Meisterschulen-am-Ostbahnhof-Munchen/ISOBUS_Hardware/Hutschienenmoped-XL/8530697758676959232-8530697224823242752-365263750140063748.png

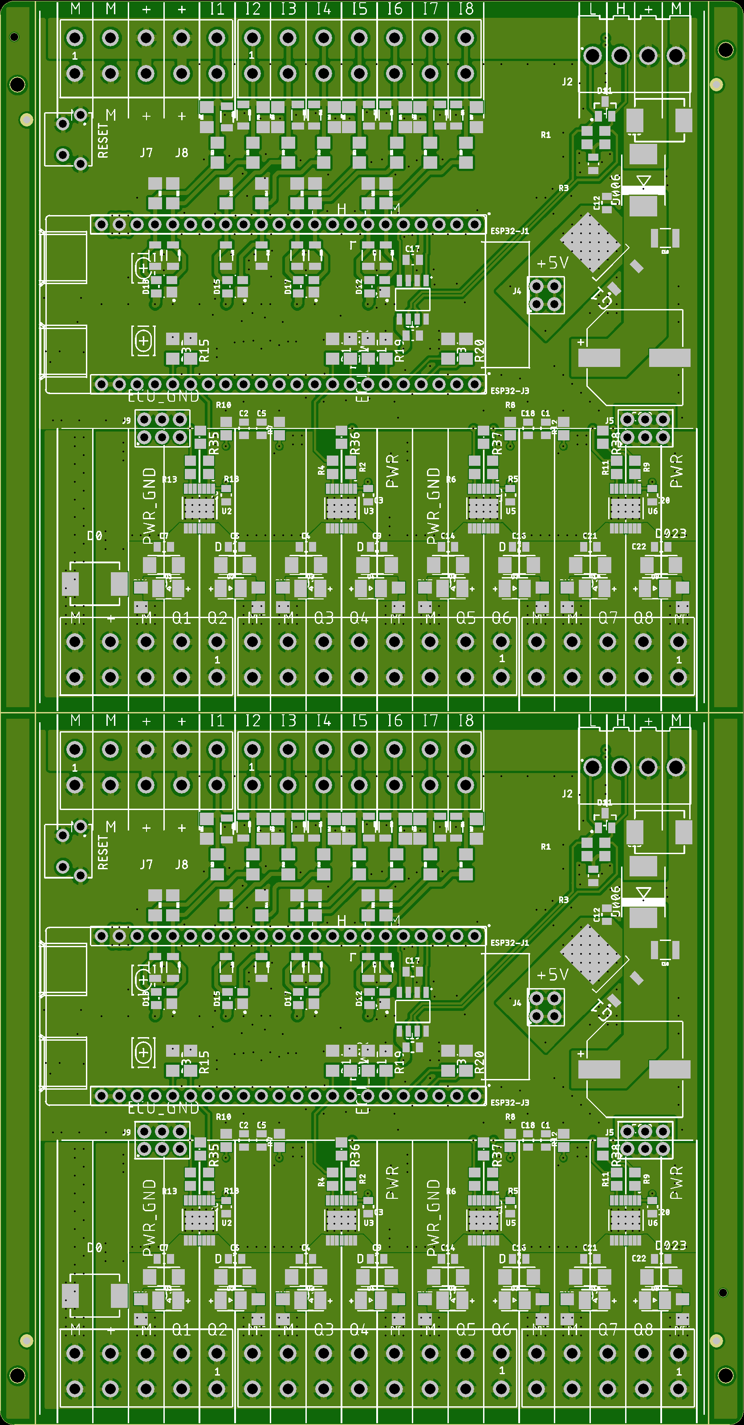
Hutschienenmoped-XL/8530697758676959232-8530697224823242752-365263750140063748.png
