Meisterschulen-am-Ostbahnhof-Munchen/ISOBUS_Hardware/Hutschienenmoped-XL/8530697765534781440-8530697225381355520-365263750140063747.png

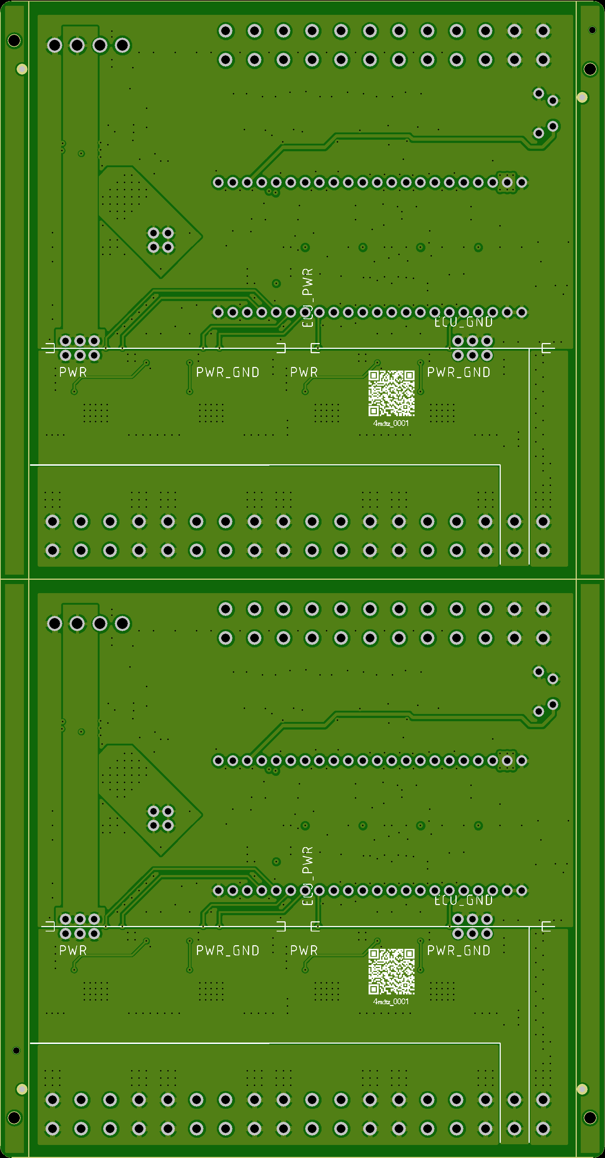
Hutschienenmoped-XL/8530697765534781440-8530697225381355520-365263750140063747.png
