Meisterschulen-am-Ostbahnhof-Munchen/ISOBUS_Hardware/XL-accessories/Board_4_Buttons/3D/Riegel rechts oben.stl

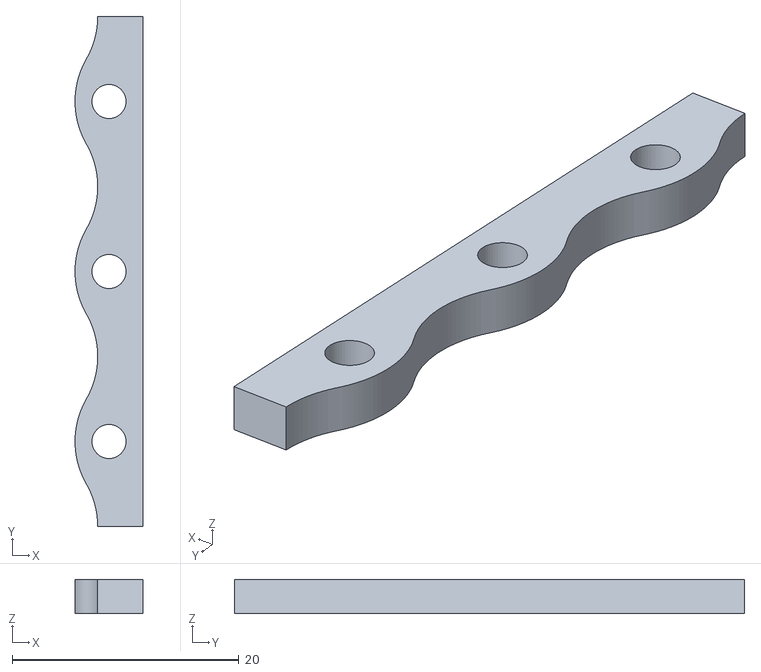
[picture p22: CAD file, 2024-10-04]
XL-accessories/Board_4_Buttons/3D/Riegel rechts oben.stl
6.00 x 45.0 x 3.00
