Meisterschulen-am-Ostbahnhof-Munchen/ISOBUS_Hardware/XL-accessories/Board_4_Buttons/Board_4_Buttons_WS-TASV.pdf

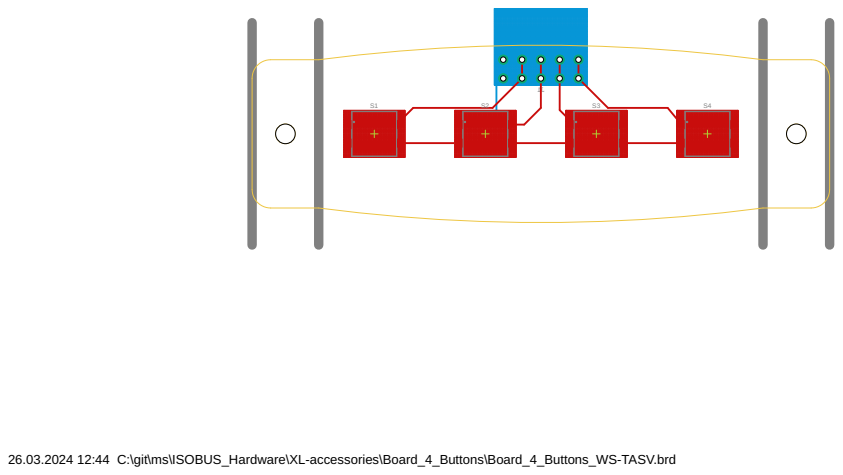
[picture p45: page 1]

26.03.2024 12:44 C:\git\ms\ISOBUS_Hardware\XL-accessories\Board_4_Buttons\Board_4_Buttons_WS-TASV.brd
