Meisterschulen-am-Ostbahnhof-Munchen/ISOBUS_Hardware/XL-accessories/Board_4_Buttons/Board_4_Buttons_WS-TATV.pdf

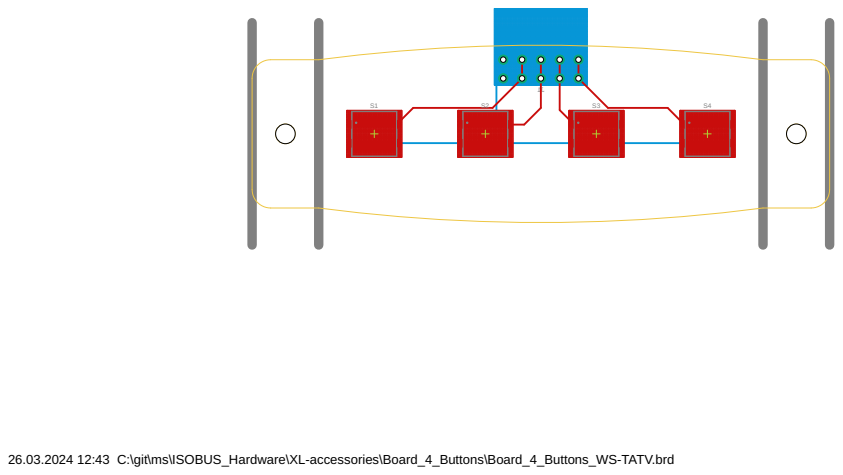
[picture p46: page 1]

26.03.2024 12:43 C:\git\ms\ISOBUS_Hardware\XL-accessories\Board_4_Buttons\Board_4_Buttons_WS-TATV.brd
