Meisterschulen-am-Ostbahnhof-Munchen/ISOBUS_Hardware/Hutschienenmoped-XL/Hauptplatine/Hauptplatine.pdf

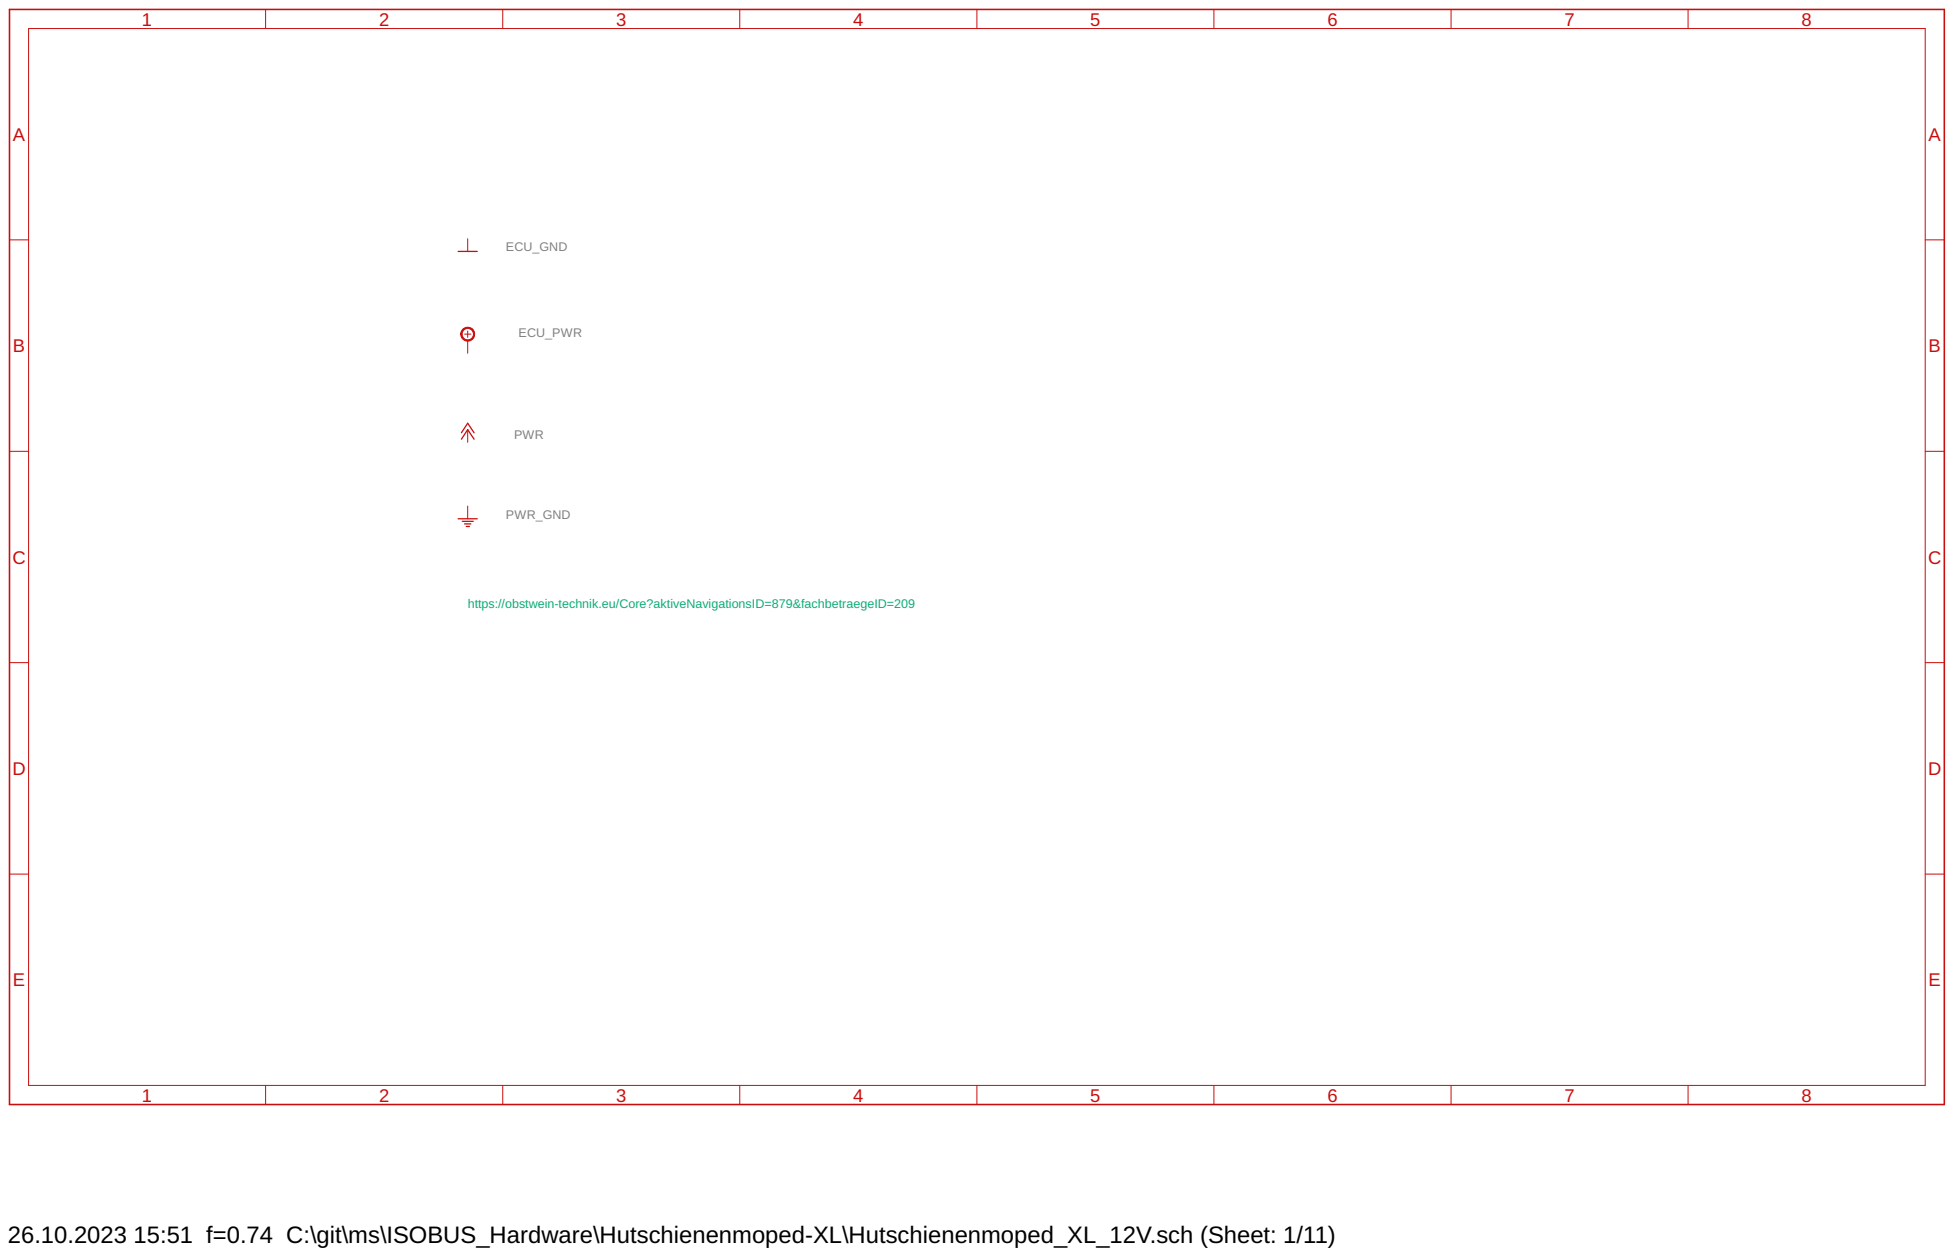
[picture p47: page 1]

https://obstwein-technik.eu/Core?aktiveNavigationsID=879&fachbetraegeID=209

26.10.2023 15:51 f=0.74 C:\git\ms\ISOBUS_Hardware\Hutschienenmoped-XL\Hutschienenmoped_XL_12V.sch (Sheet: 1/11)

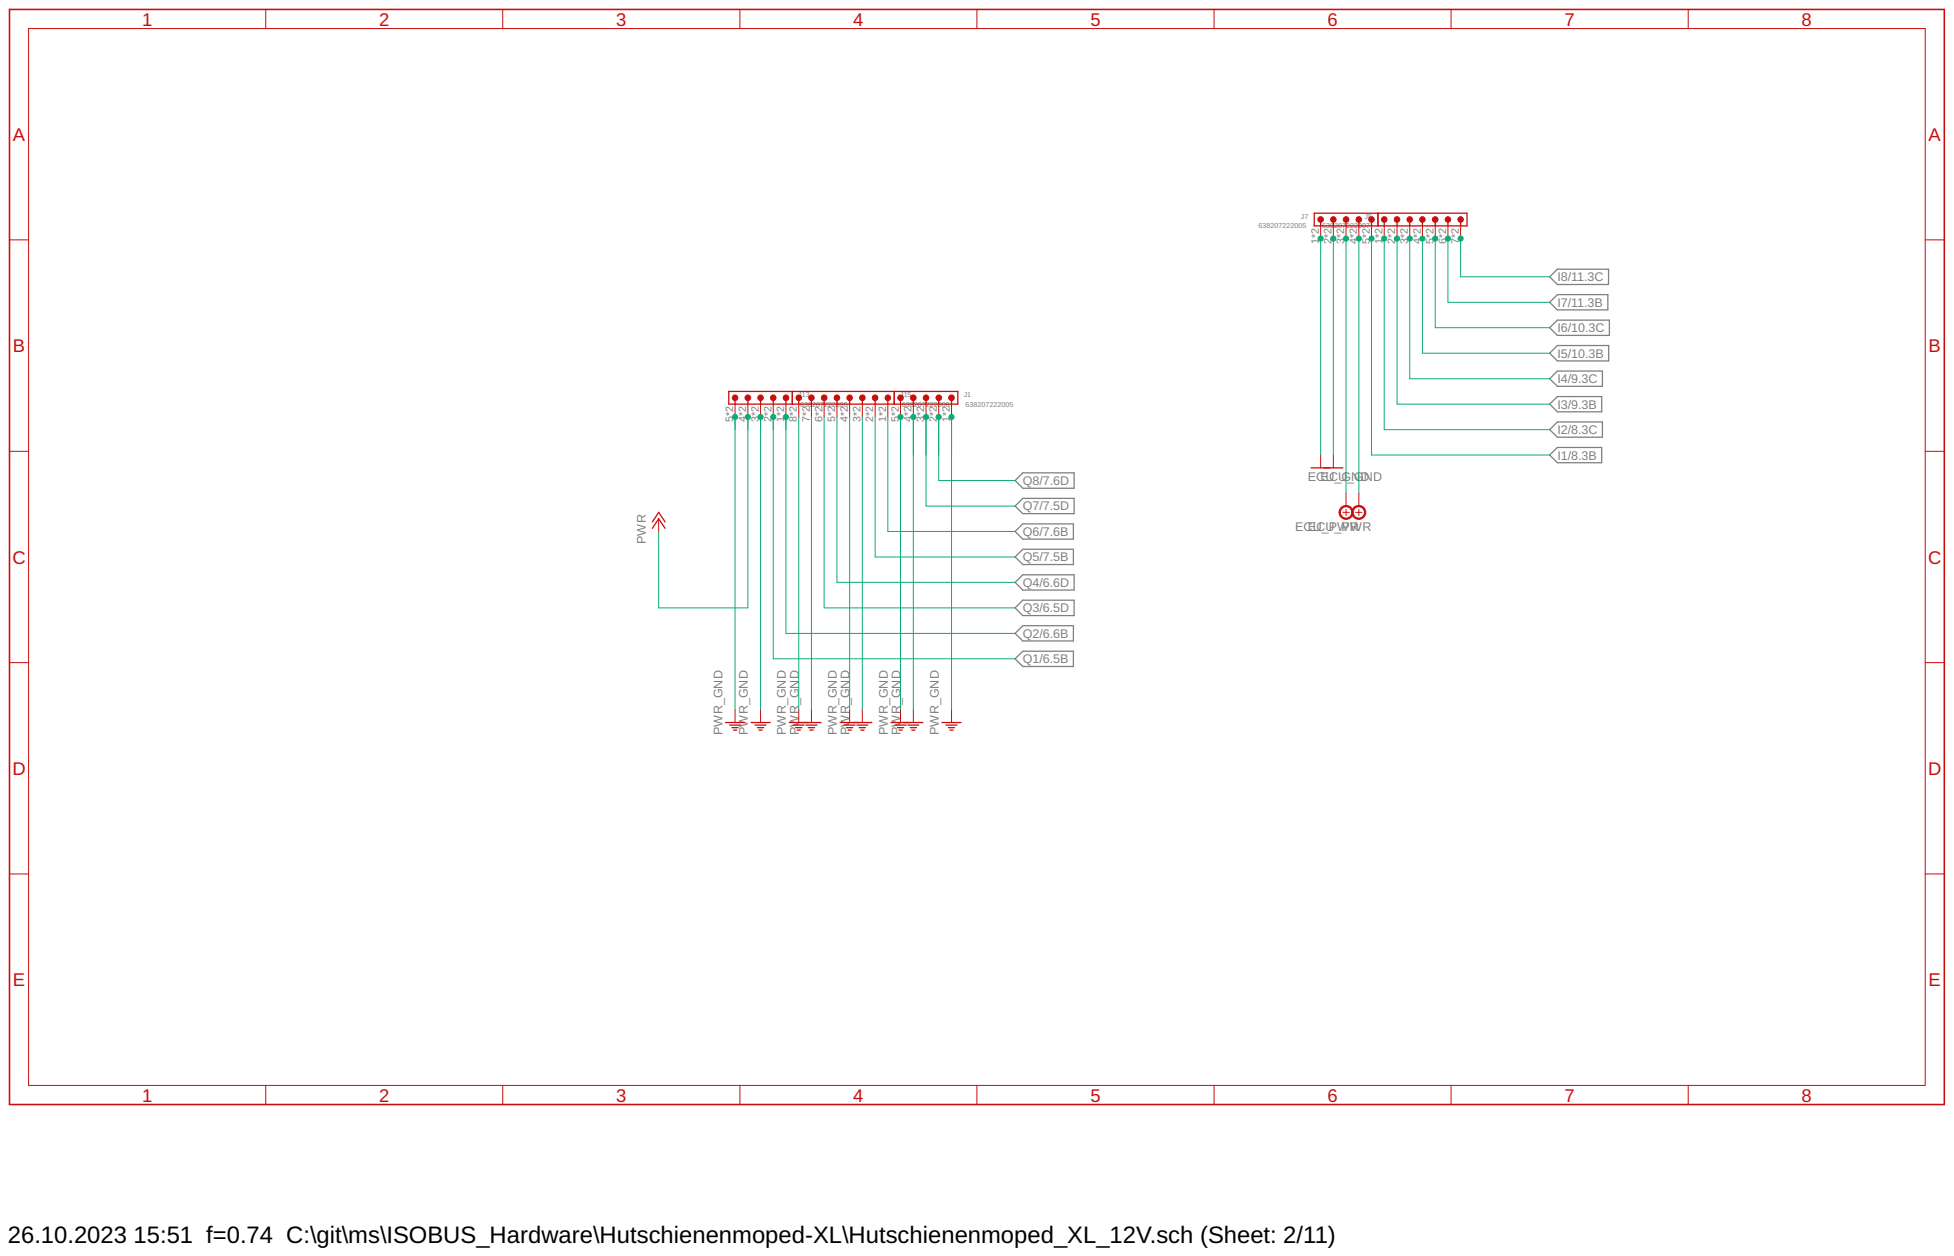
[picture p48: page 2]

26.10.2023 15:51 f=0.74 C:\git\ms\ISOBUS_Hardware\Hutschienenmoped-XL\Hutschienenmoped_XL_12V.sch (Sheet: 2/11)

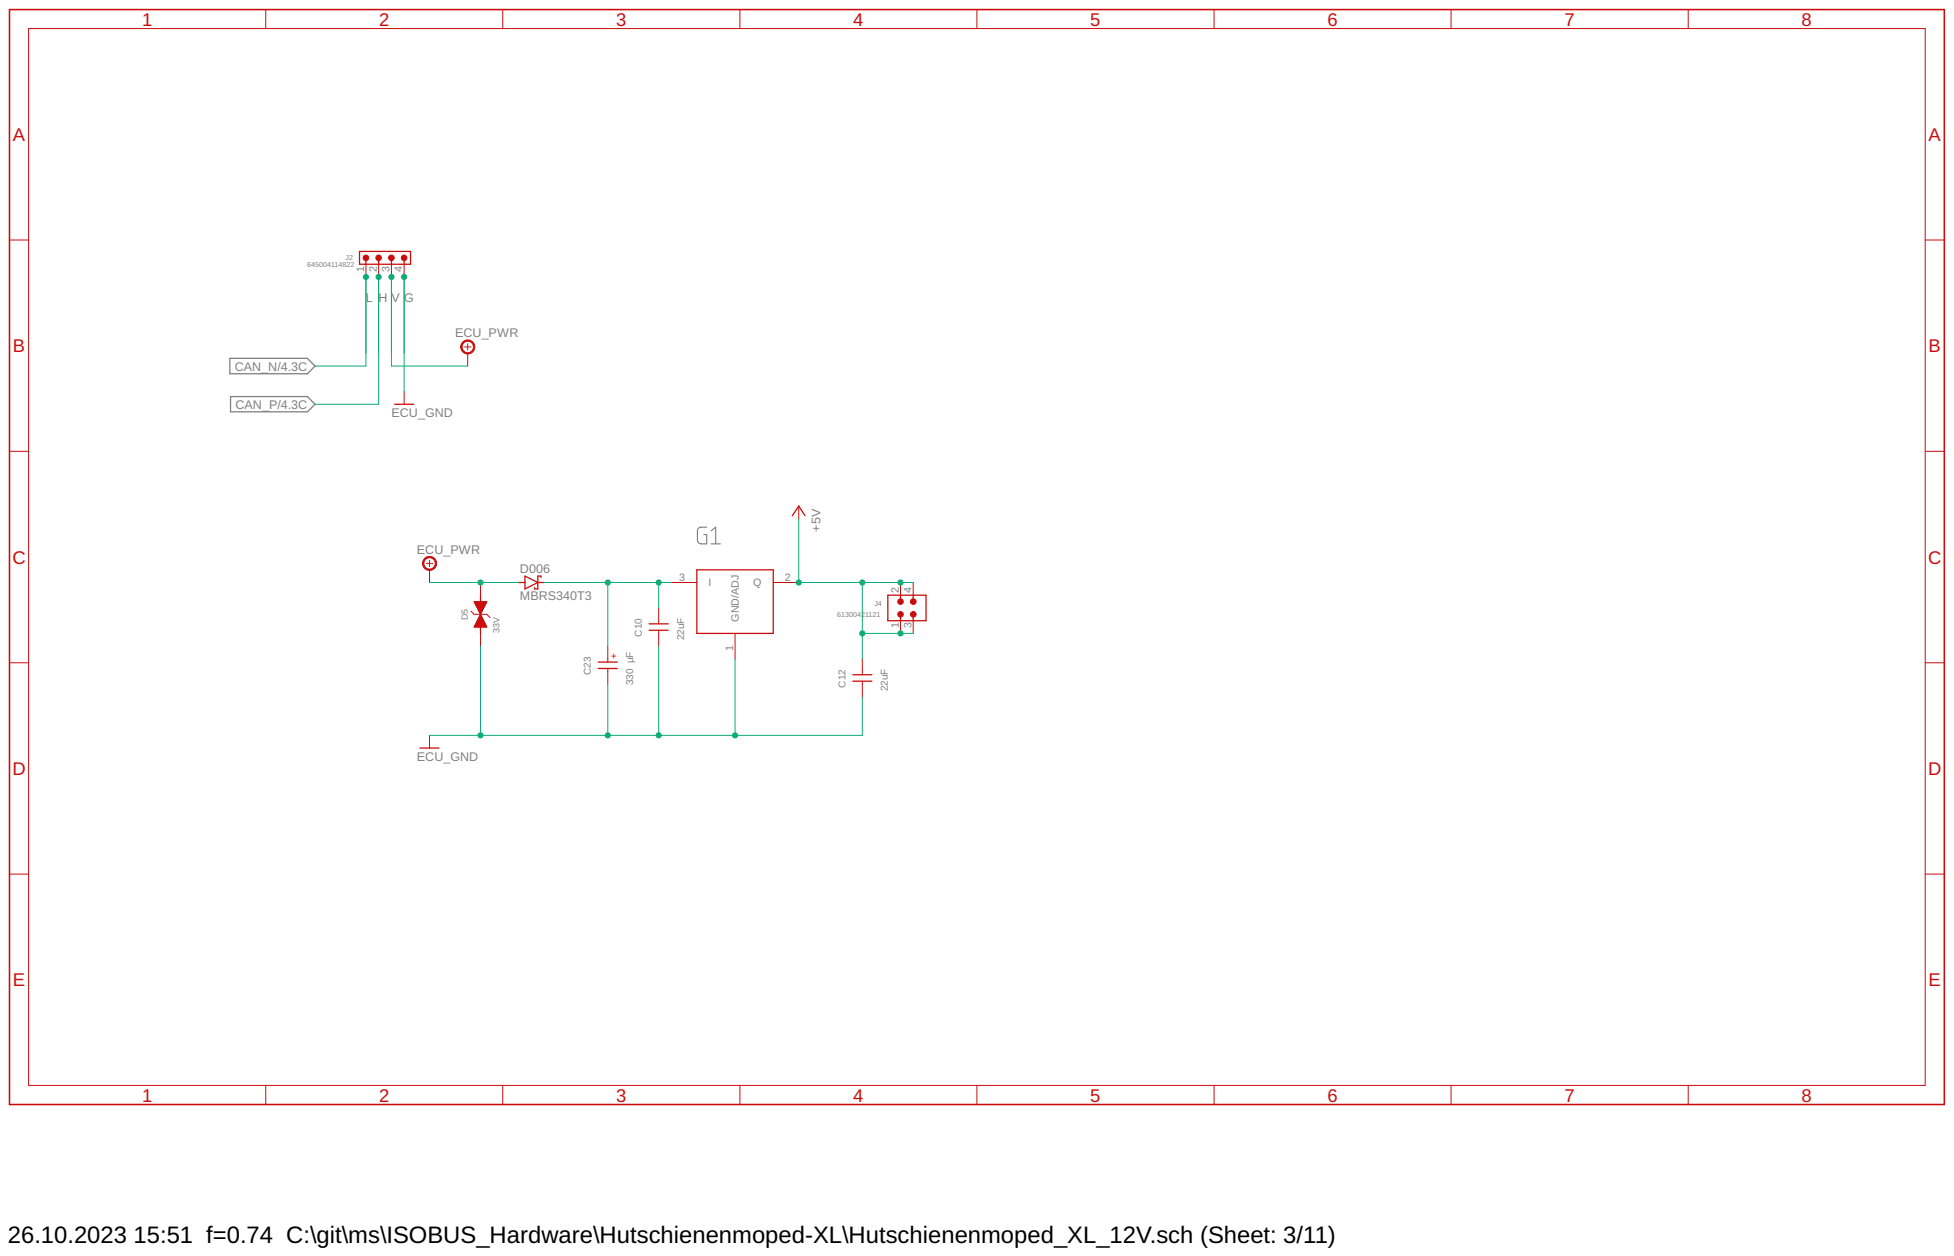
[picture p49: page 3]

26.10.2023 15:51 f=0.74 C:\git\ms\ISOBUS_Hardware\Hutschienenmoped-XL\Hutschienenmoped_XL_12V.sch (Sheet: 3/11)

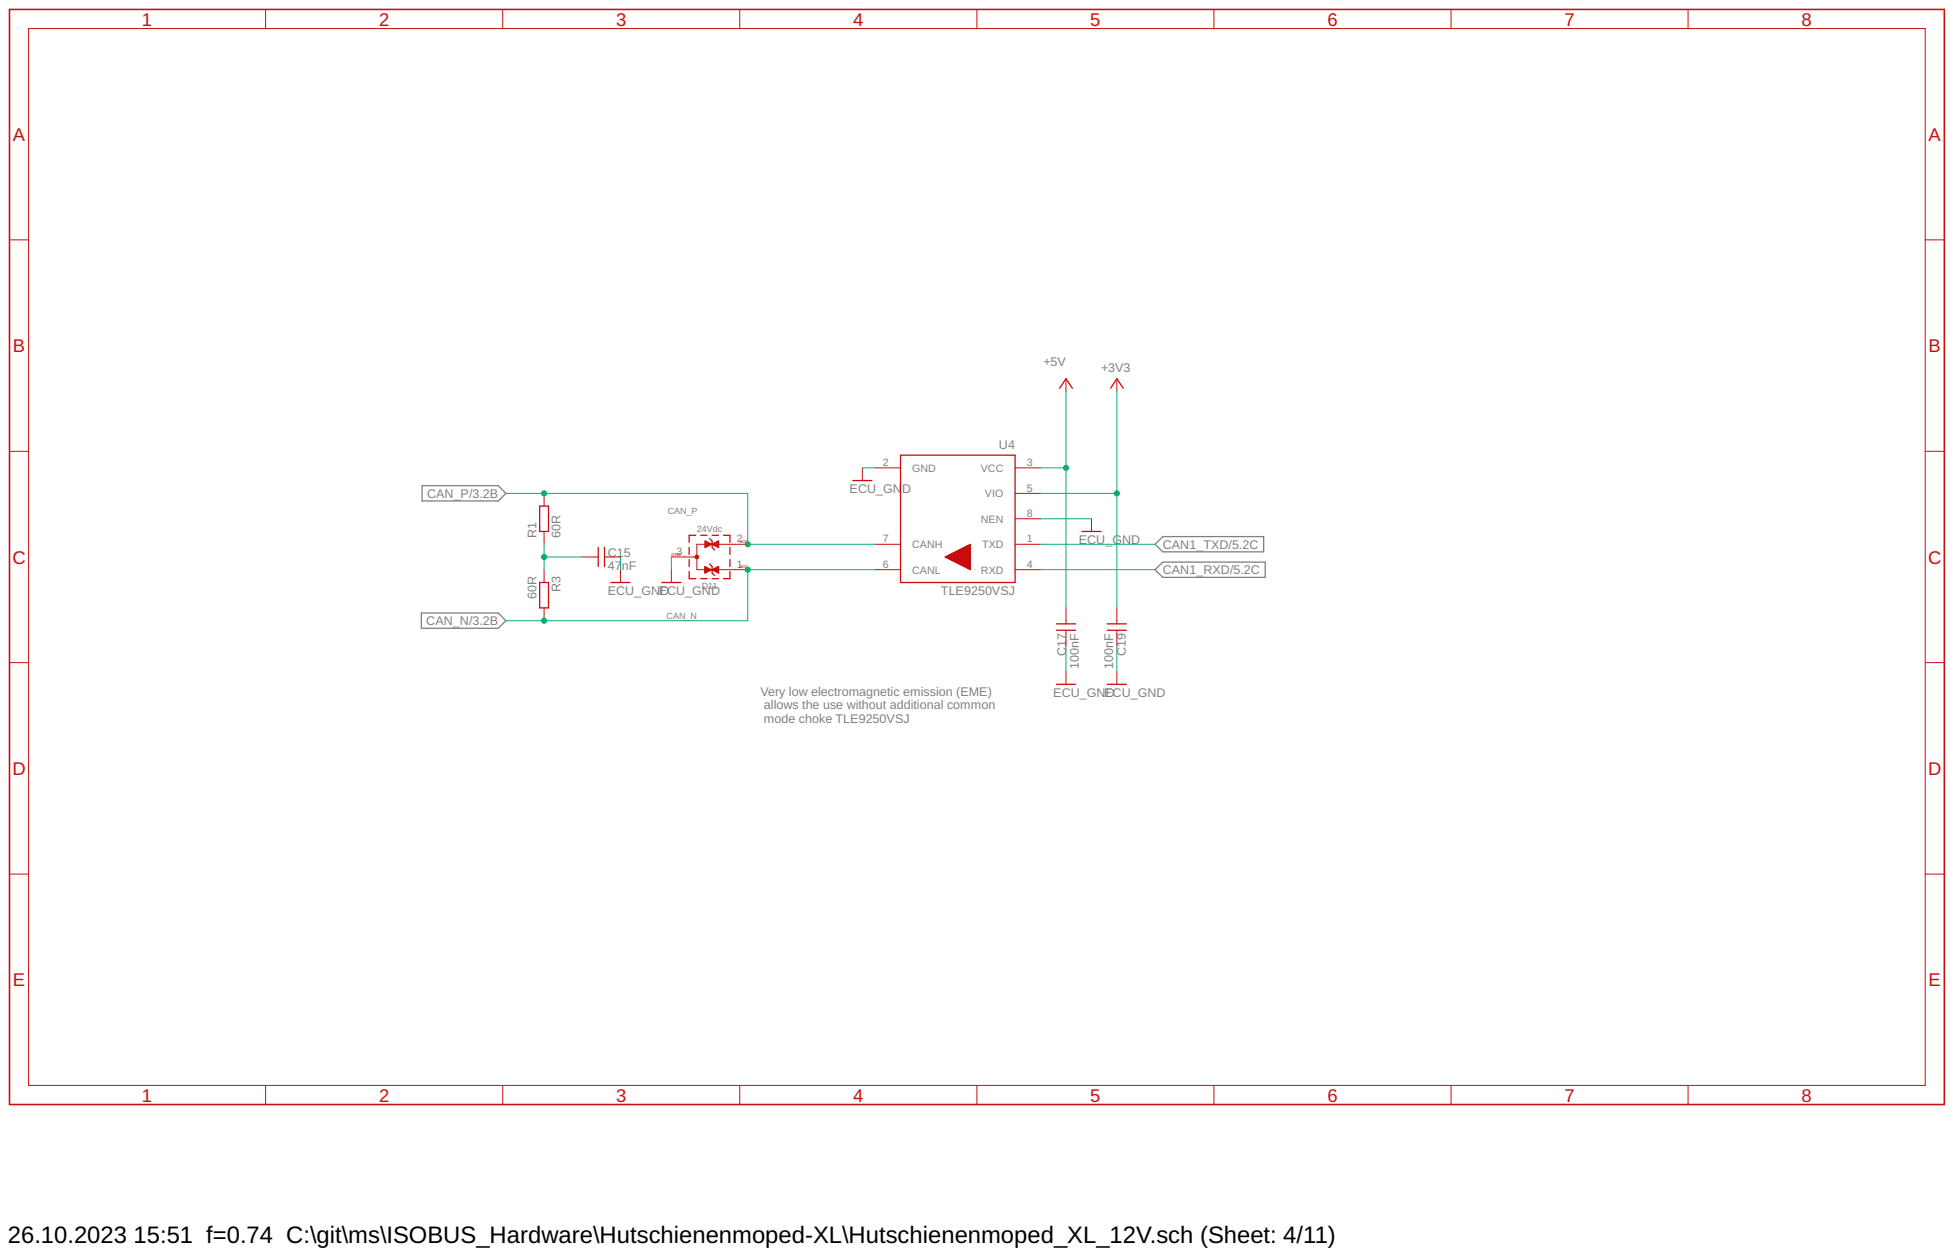
[picture p50: page 4]

Very low electromagnetic emission (EME) allows the use without additional common mode choke TLE9250VSJ

26.10.2023 15:51 f=0.74 C:\git\ms\ISOBUS_Hardware\Hutschienenmoped-XL\Hutschienenmoped_XL_12V.sch (Sheet: 4/11)

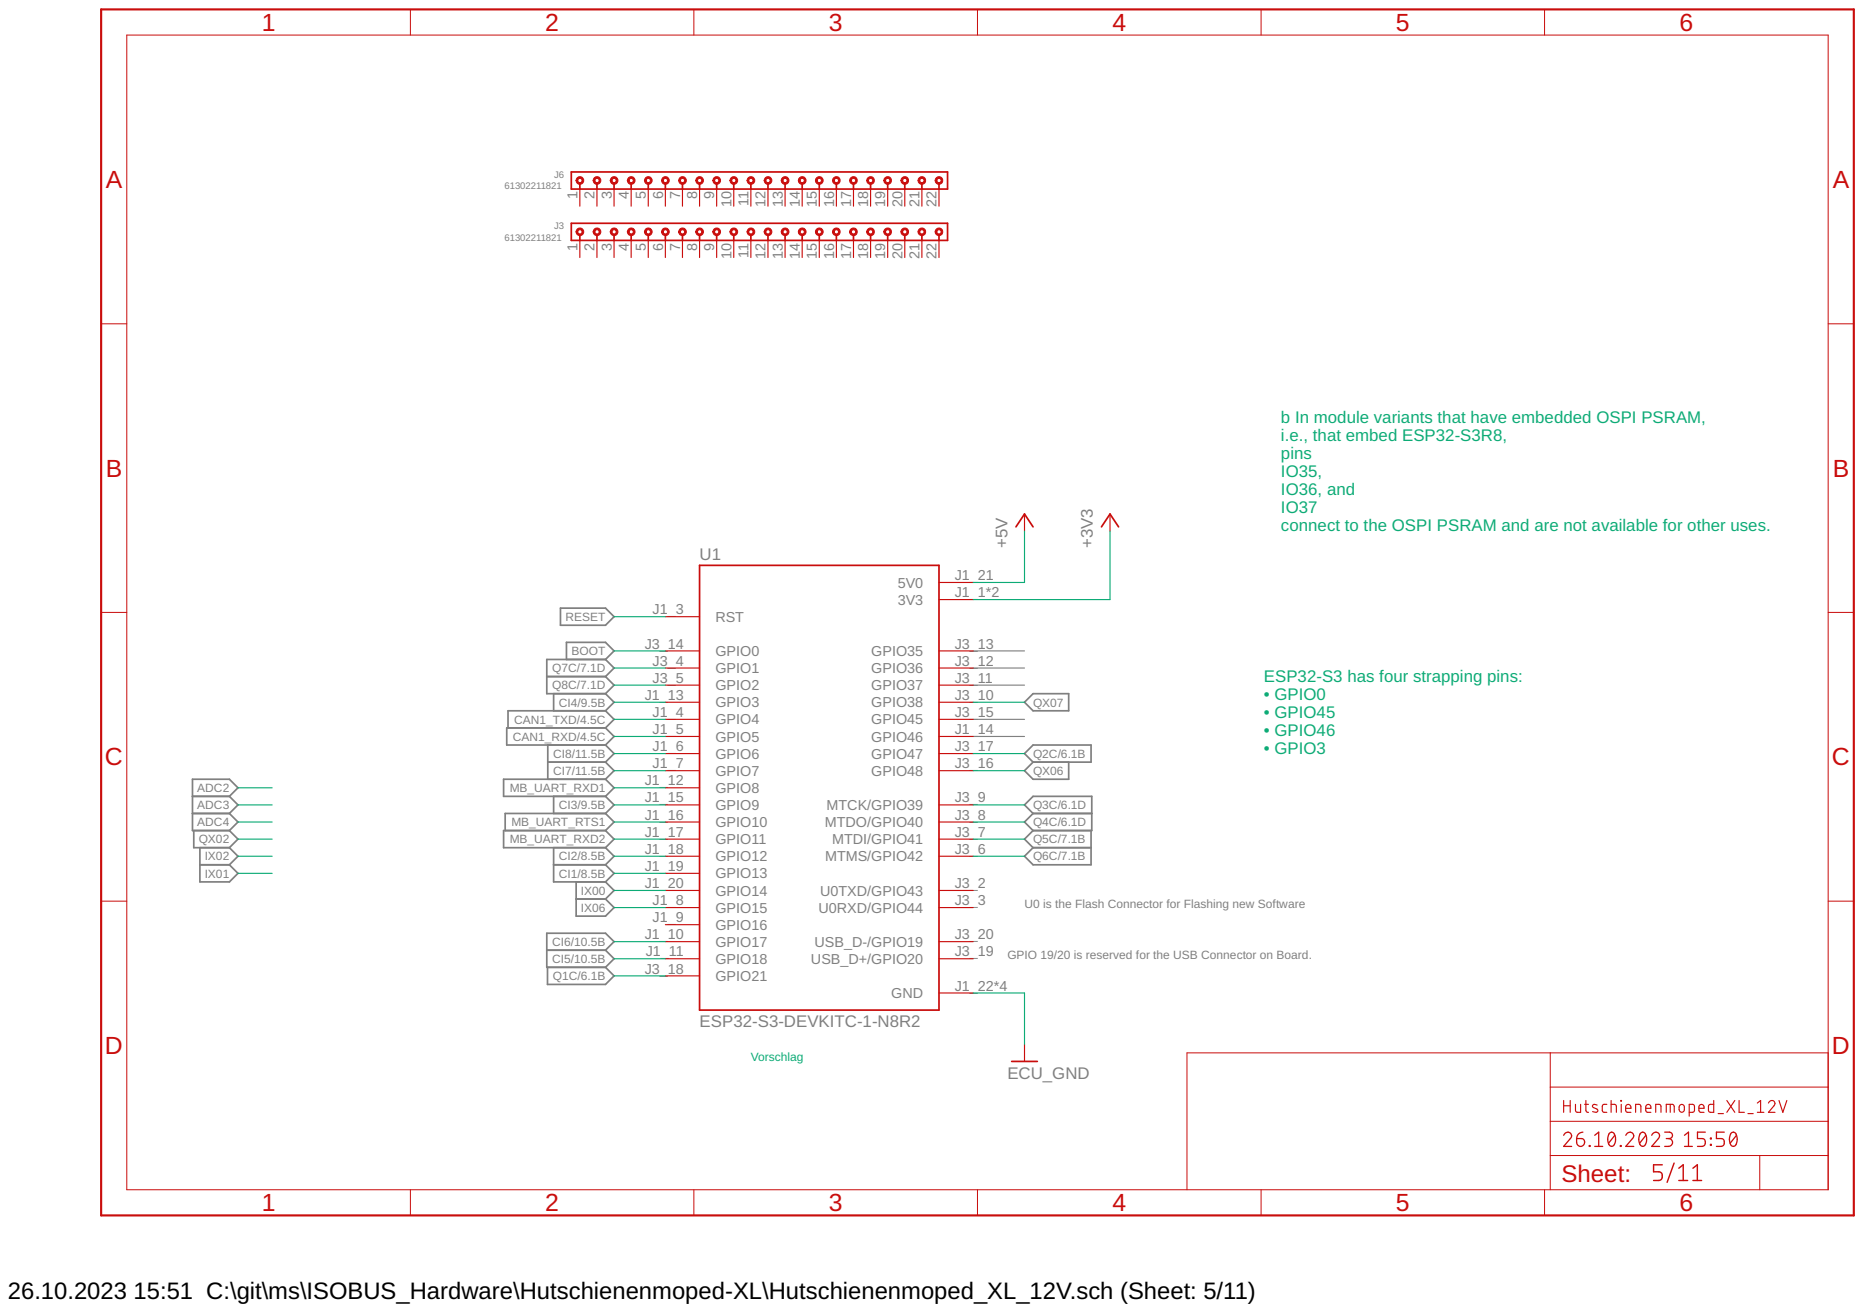
[picture p51: page 5]

b In module variants that have embedded OSPI PSRAM,
i.e., that embed ESP32-S3R8, pins

IO36, and
connect to the OSPI PSRAM and are not available for other uses.

ESP32-S3 has four strapping pins: • GPIO0

GPIO 19/20 is reserved for the USB Connector on Board. U0 is the Flash Connector for Flashing new Software ESP32-S3-DEVKITC-1-N8R2

26.10.2023 15:51 C:\git\ms\ISOBUS_Hardware\Hutschienenmoped-XL\Hutschienenmoped_XL_12V.sch (Sheet: 5/11)

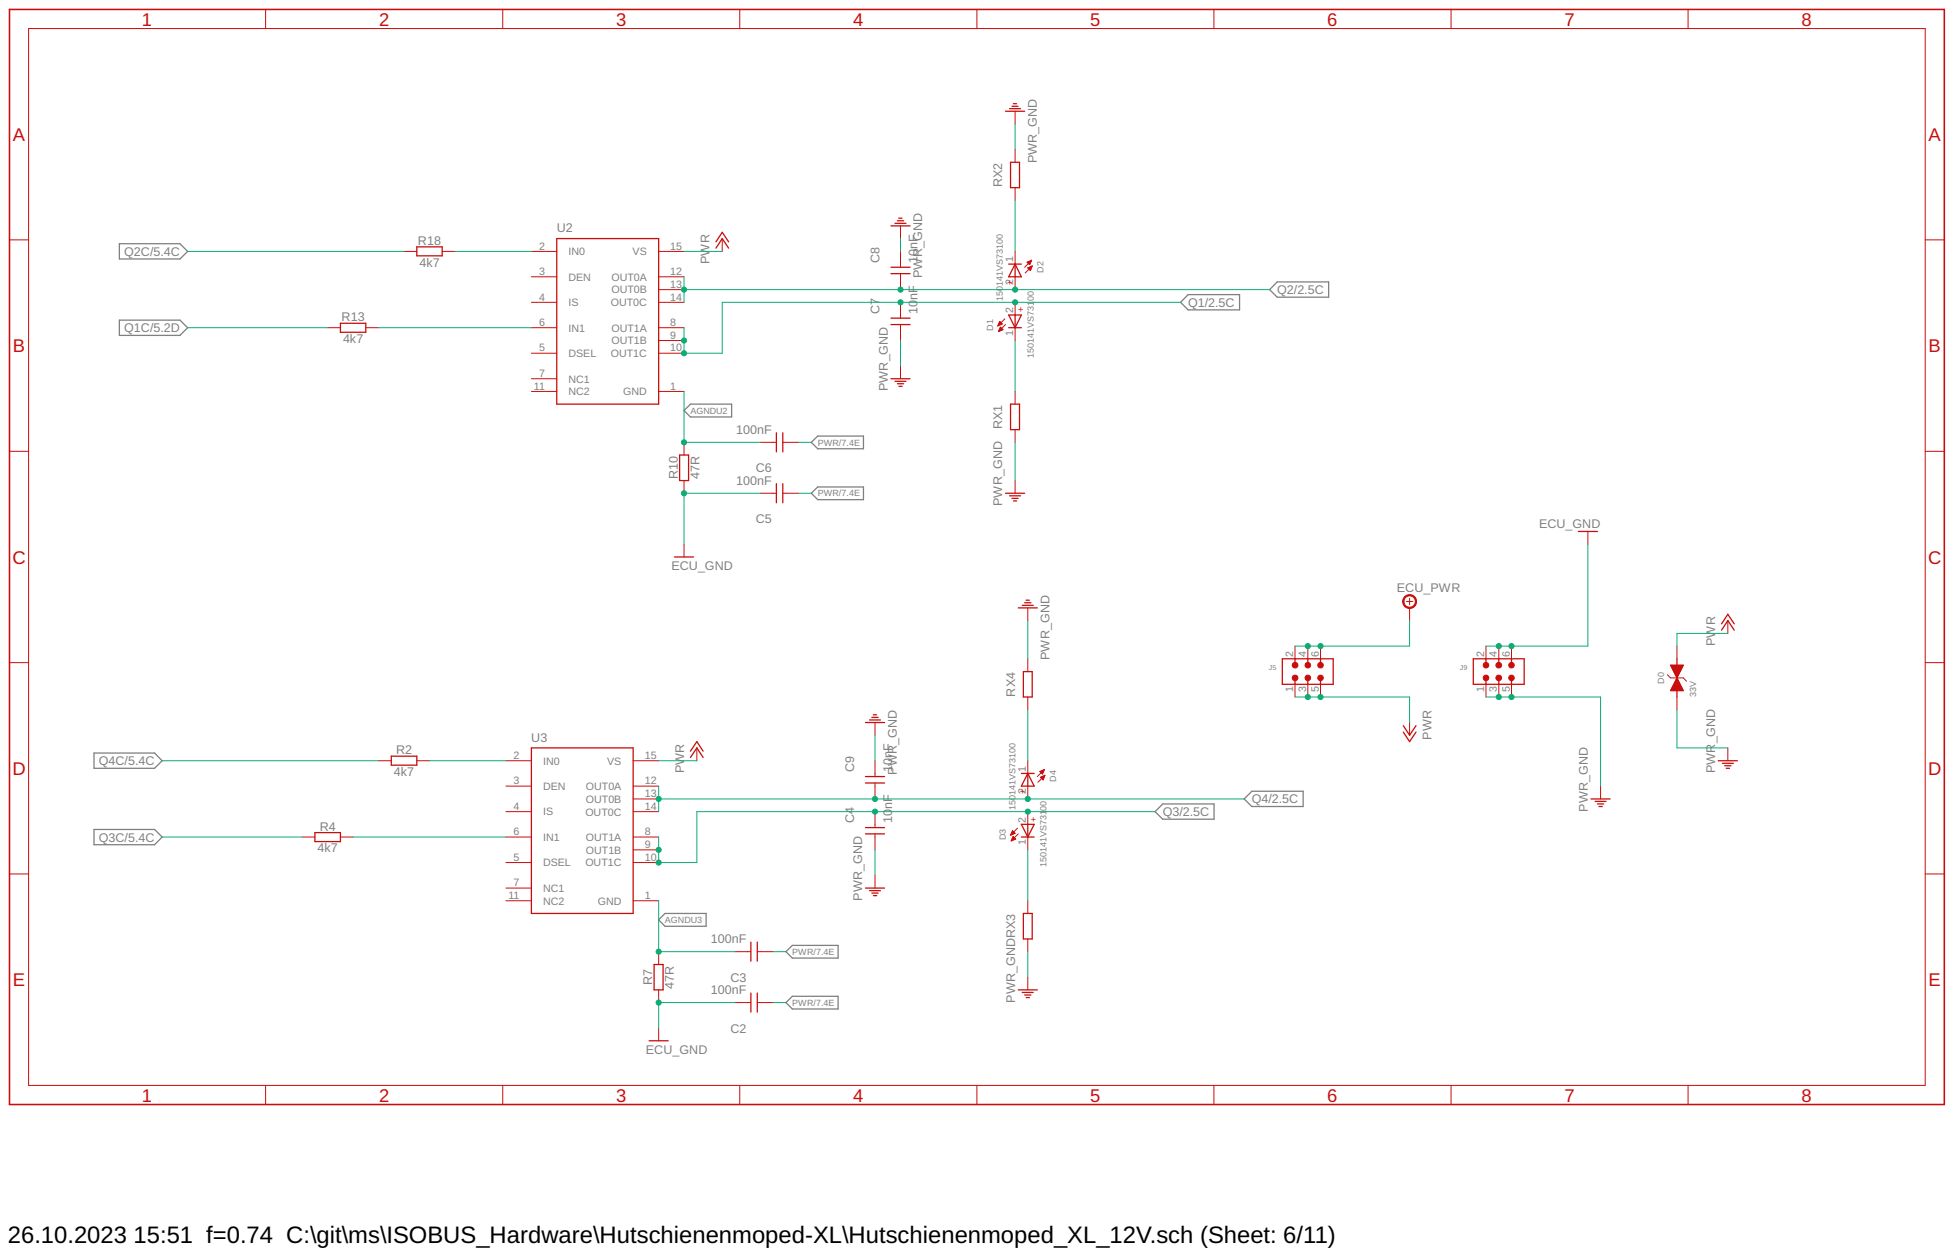
[picture p52: page 6]

26.10.2023 15:51 f=0.74 C:\git\ms\ISOBUS_Hardware\Hutschienenmoped-XL\Hutschienenmoped_XL_12V.sch (Sheet: 6/11)

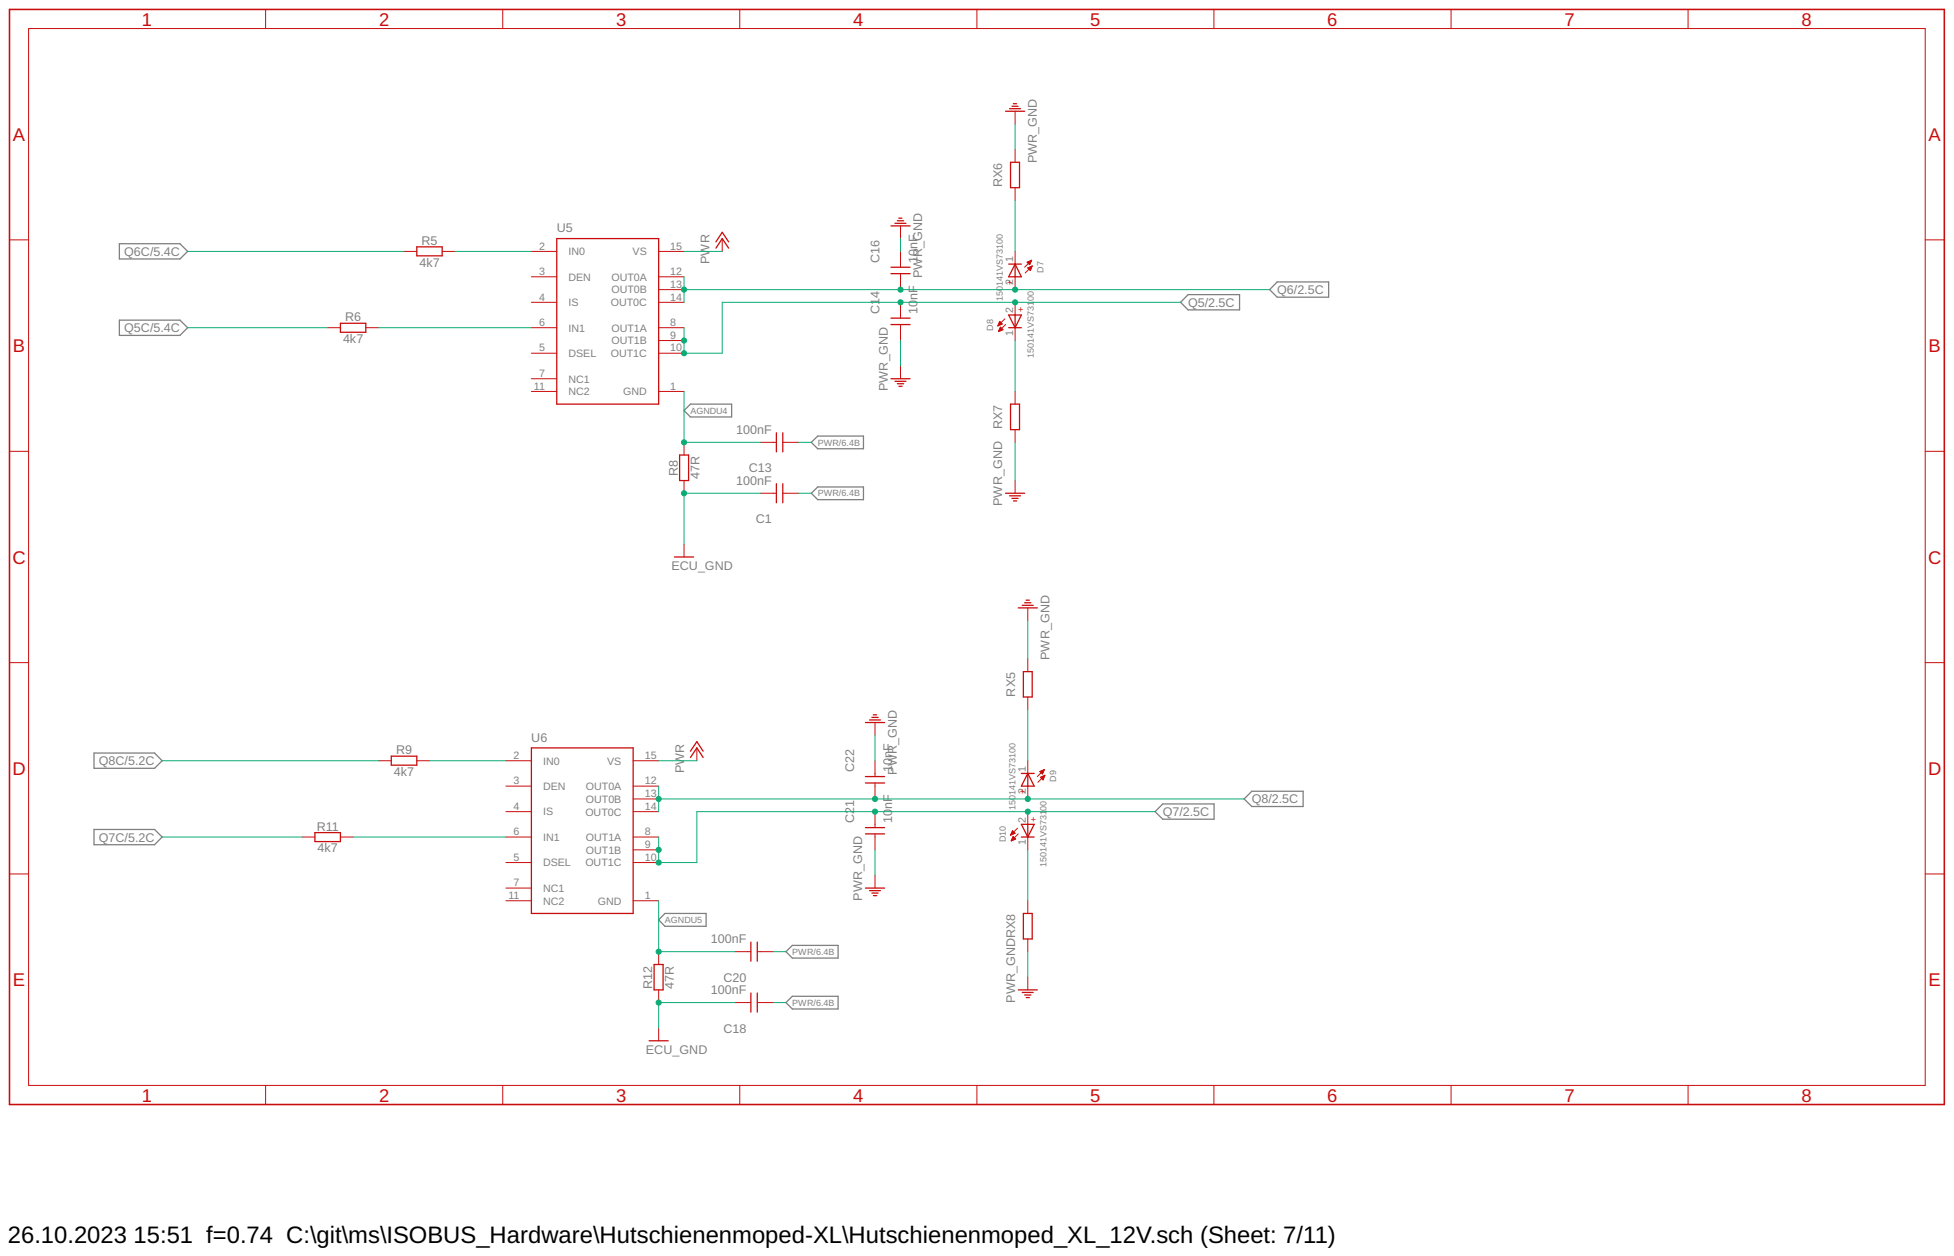
[picture p53: page 7]

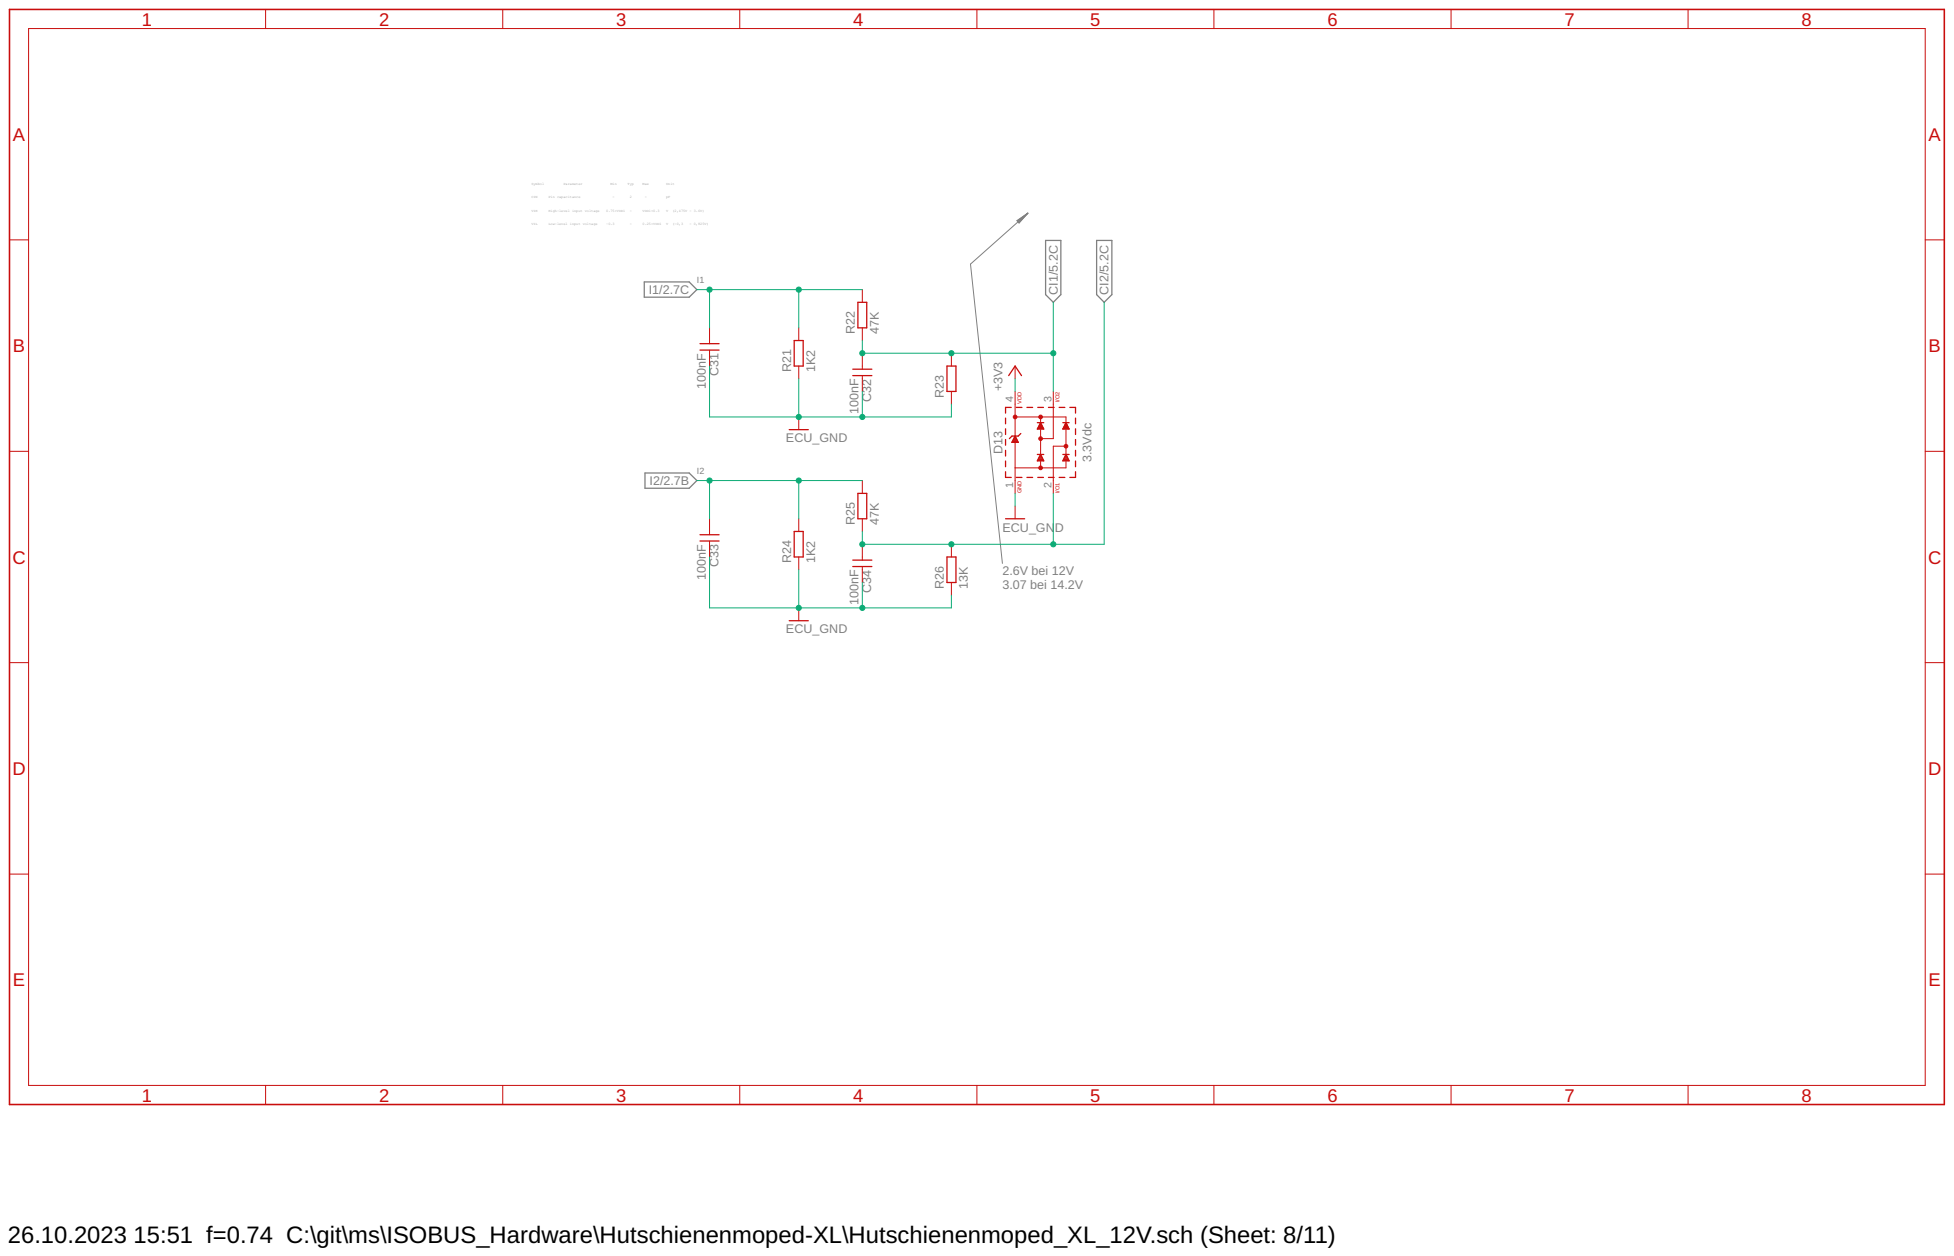
[picture p54: page 8]

26.10.2023 15:51 f=0.74 C:\git\ms\ISOBUS_Hardware\Hutschienenmoped-XL\Hutschienenmoped_XL_12V.sch (Sheet: 8/11)

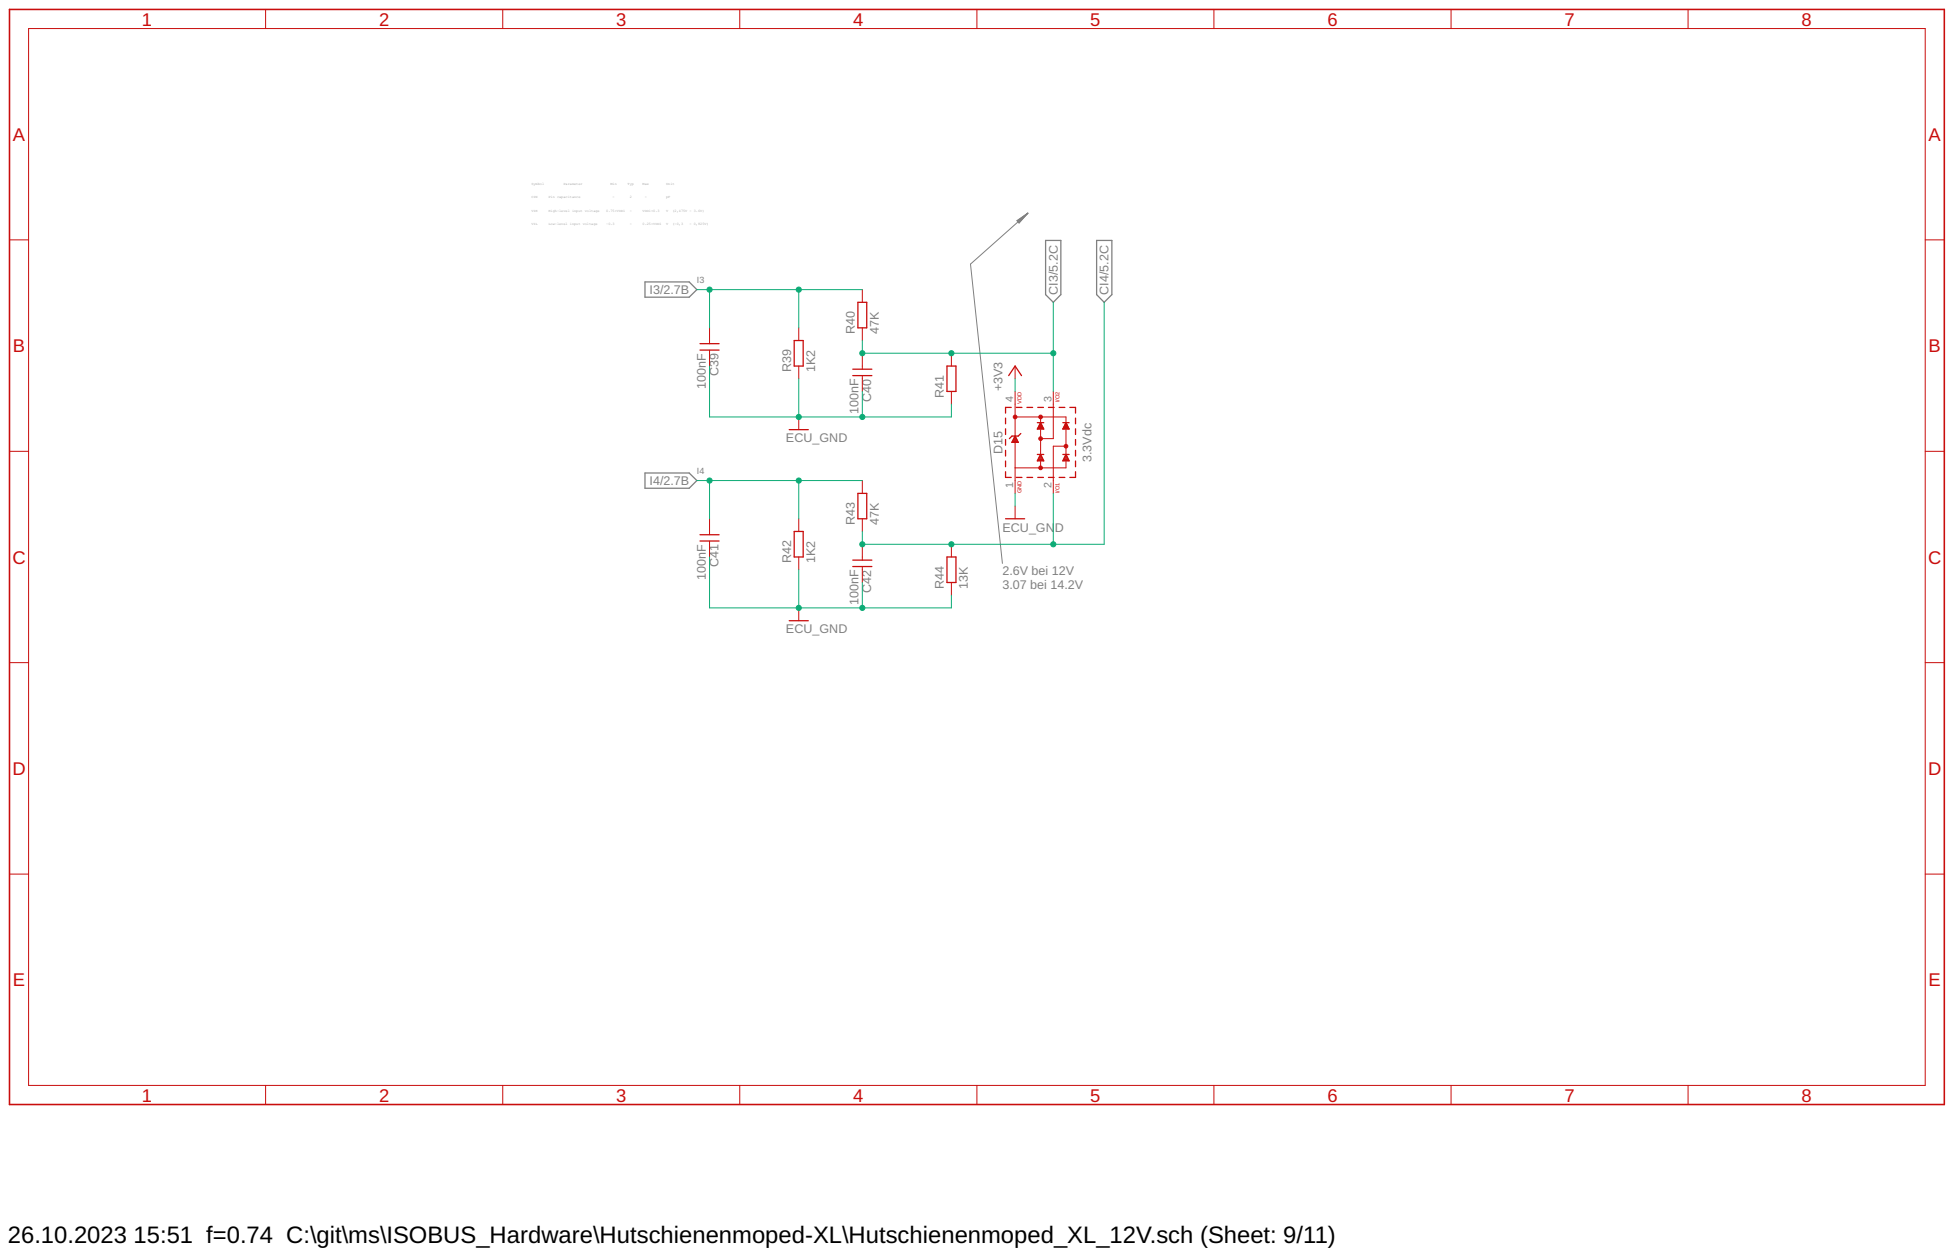
[picture p55: page 9]

26.10.2023 15:51 f=0.74 C:\git\ms\ISOBUS_Hardware\Hutschienenmoped-XL\Hutschienenmoped_XL_12V.sch (Sheet: 9/11)

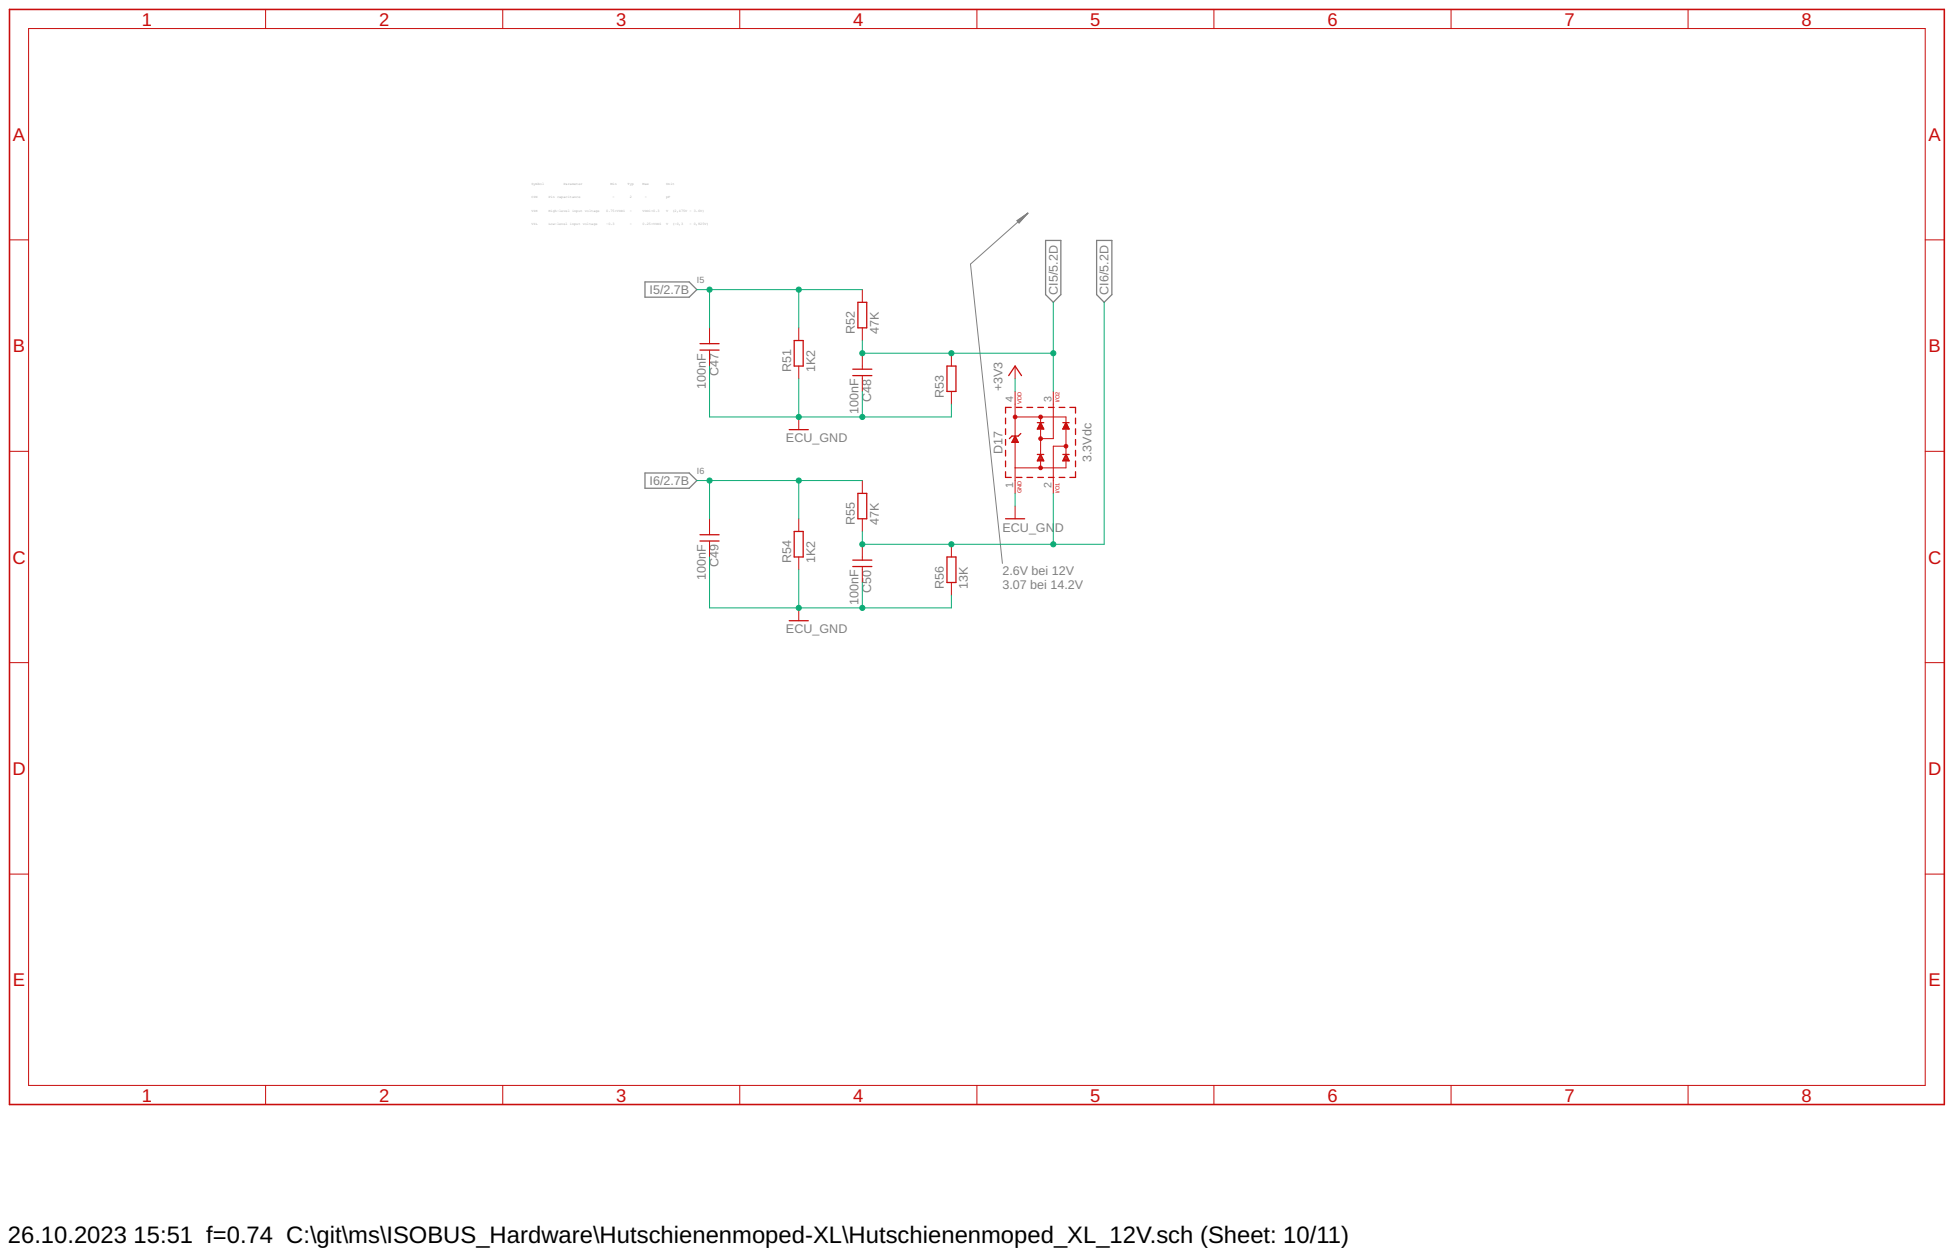
[picture p56: page 10]

26.10.2023 15:51 f=0.74 C:\git\ms\ISOBUS_Hardware\Hutschienenmoped-XL\Hutschienenmoped_XL_12V.sch (Sheet: 10/11)

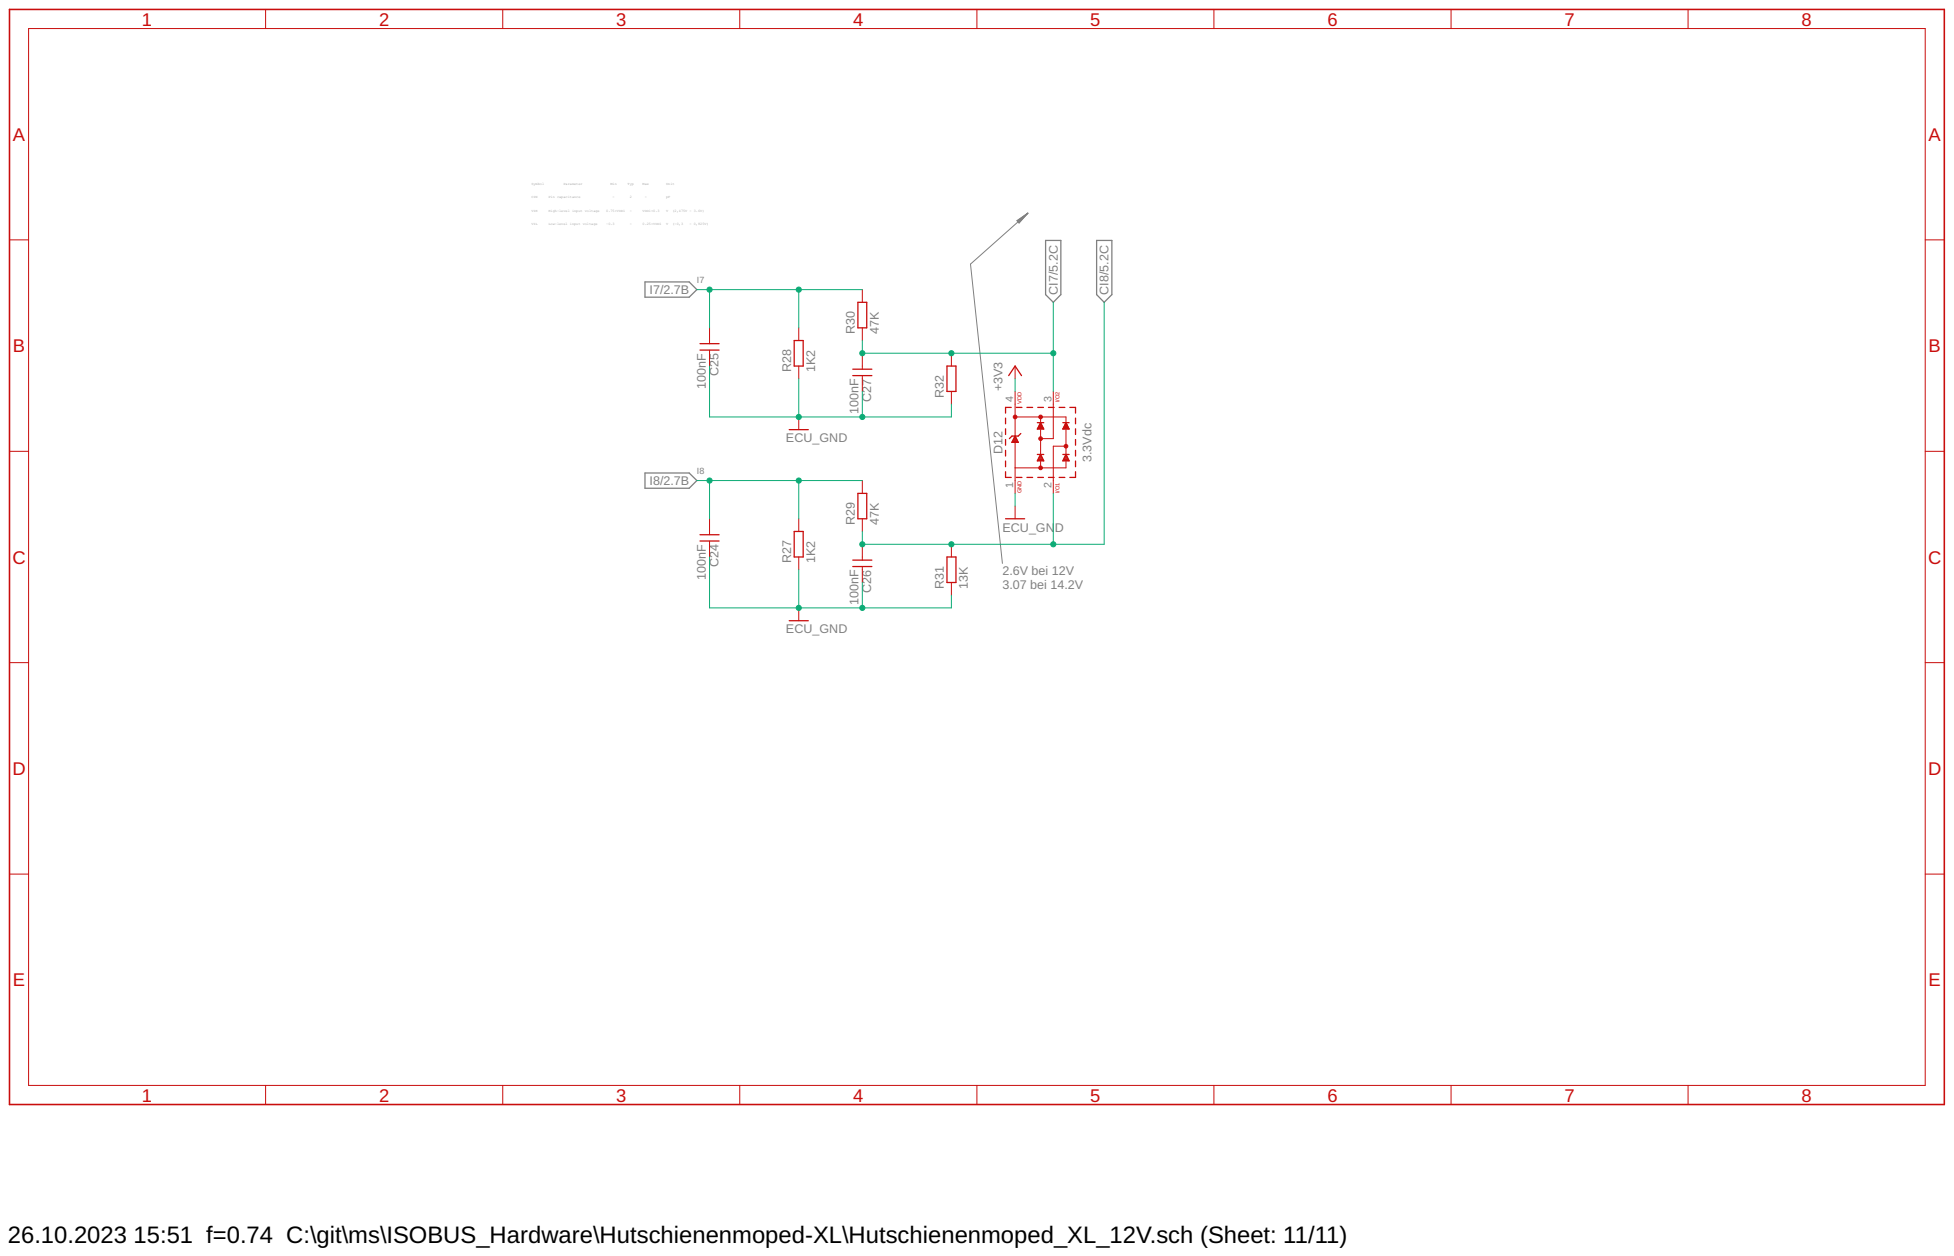
[picture p57: page 11]

26.10.2023 15:51 f=0.74 C:\git\ms\ISOBUS_Hardware\Hutschienenmoped-XL\Hutschienenmoped_XL_12V.sch (Sheet: 11/11)
