Meisterschulen-am-Ostbahnhof-Munchen/ISOBUS_Hardware/Hutschienenmoped-XL/Symbol/Hutschienenmoped_XL_12V_SYMB.pdf

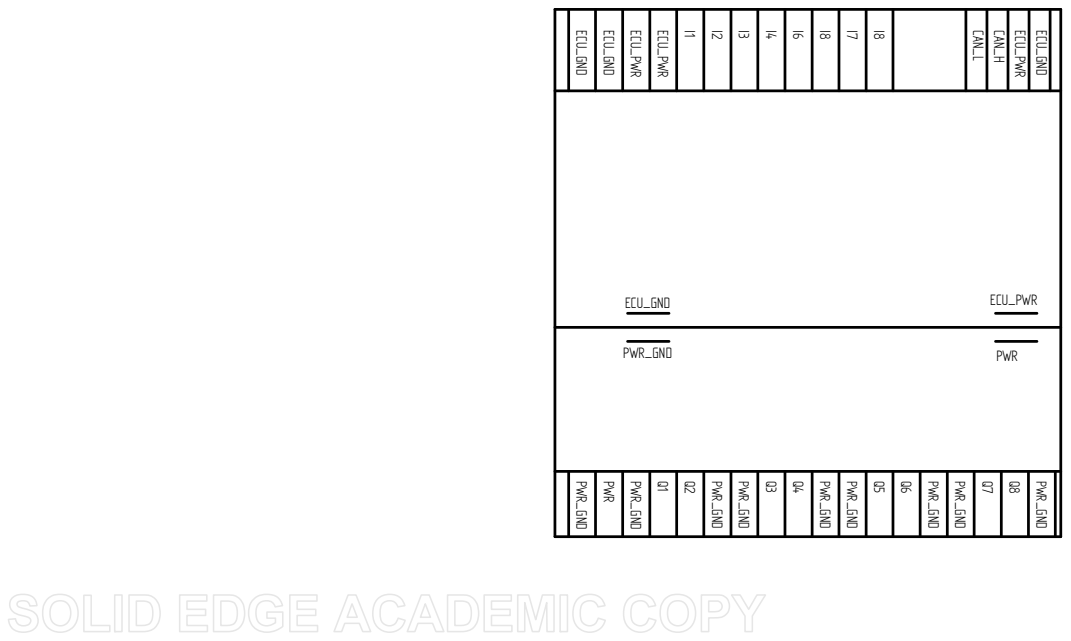
[picture p73: page 1]
