Meisterschulen-am-Ostbahnhof-Munchen/ISOBUS_Hardware/Hutschienenmoped/Hutschienenmoped_24V.brd

## EAGLE design Hutschienenmoped/Hutschienenmoped_24V.brd (2023-10-20)


Notes on the sheet:
https://obstwein-technik.eu/Core?aktiveNavigationsID=879&fachbetraegeID=209

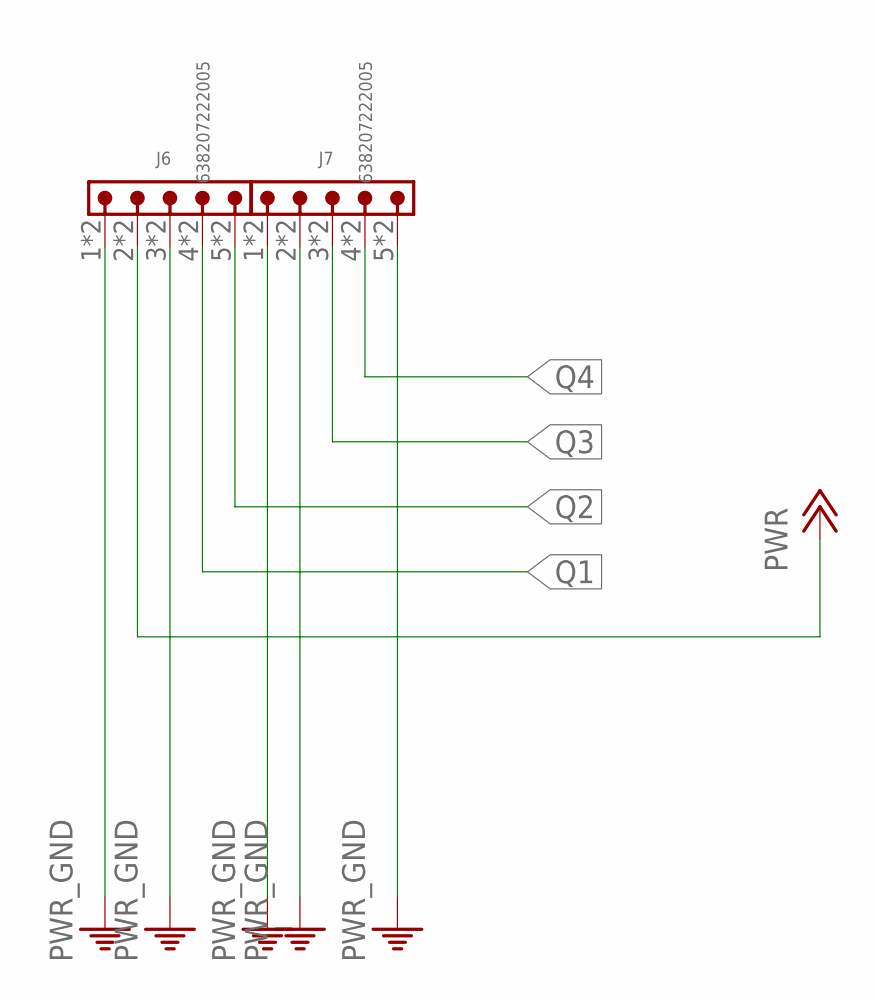
[picture p93: schematic Hutschienenmoped_24V.sch, sheet 2]

Parts:
J6, J7: 638207222005

Connections:
PWR: J6.2, J6.A2 (2); also elsewhere on the board
PWR_GND: J6.1, J6.3, J6.A1 (1), J6.A3 (3), J7.1, J7.2, J7.5, J7.A1 (1), J7.A2 (2), J7.A5 (5); also elsewhere on the board
Q1: J6.4, J6.A4 (4); also elsewhere on the board
Q2: J6.5, J6.A5 (5); also elsewhere on the board
Q3: J7.3, J7.A3 (3); also elsewhere on the board
Q4: J7.4, J7.A4 (4); also elsewhere on the board

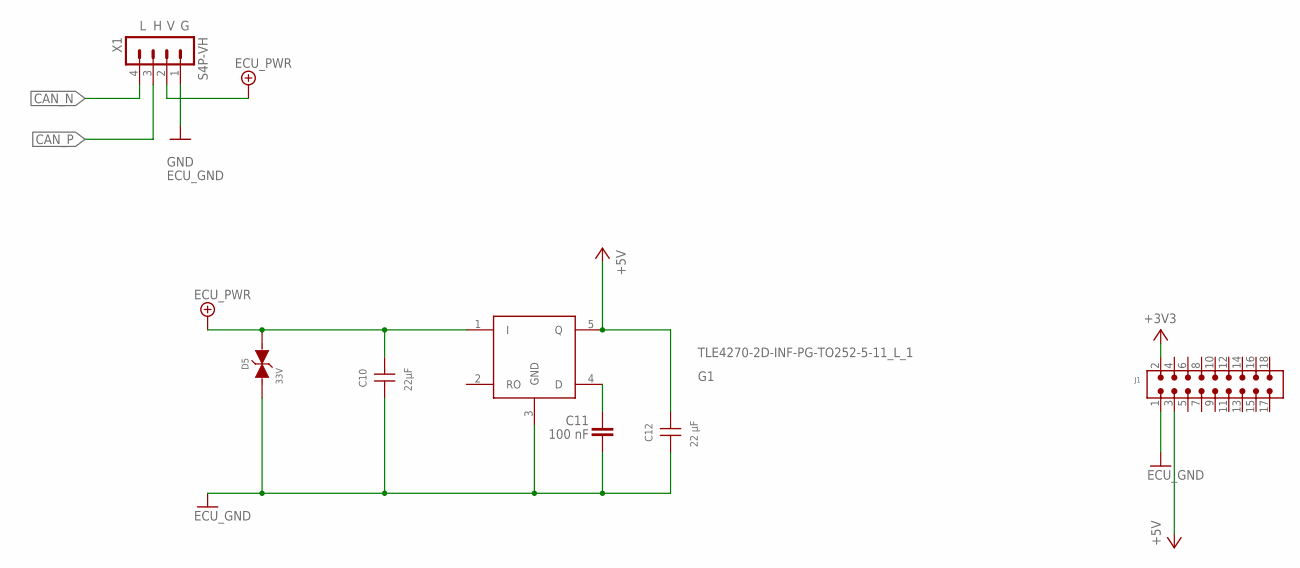
[picture p94: schematic Hutschienenmoped_24V.sch, sheet 3]

Parts:
C10: 22µF; WCAP-CSGP_1210_H2.5
C11: 100 nF; WCAP-CSGP_0402
C12: 22 µF; WCAP-CSGP_0805_H1.25_R
D5: 33V; WE-TVSP_DO-214AB_BIDIRECTIONAL
G1: TLE4270-2D-INF-PG-TO252-5-11_L_1; INF-PG-TO252-5-11_L_1PRIMARY
J1: 6130XX21121_61301821121; 61301821121
X1: S4P-VH

Connections:
+3V3: J1.2; also elsewhere on the board
+5V: C12.2, G1.5 (Q), J1.3; also elsewhere on the board
CAN_N: X1.4; also elsewhere on the board
CAN_P: X1.3; also elsewhere on the board
ECU_GND: C10.1, C11.2, C12.1, D5.1, G1.3 (GND), J1.1, X1.1; also elsewhere on the board
ECU_PWR: C10.2, D5.2, G1.1 (I), X1.2; also elsewhere on the board
unnamed: C11.1, G1.4 (D)

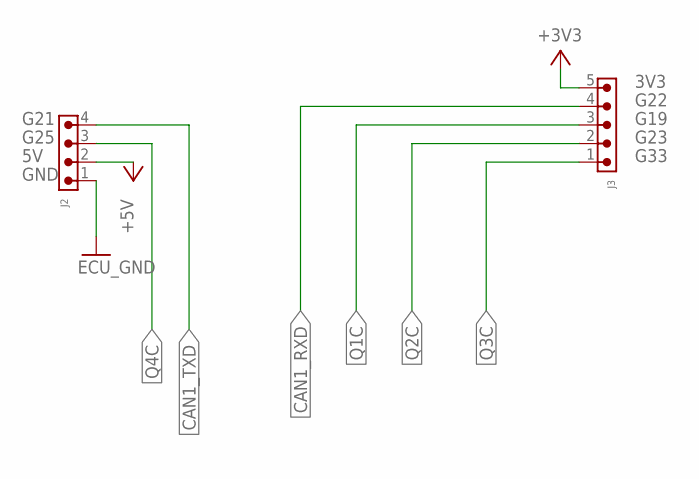
[picture p95: schematic Hutschienenmoped_24V.sch, sheet 4]

Parts:
J2: 6130XX11121_61300411121; 61300411121
J3: 6130XX11121_61300511121; 61300511121

Connections:
+3V3: J3.5; also elsewhere on the board
+5V: J2.2; also elsewhere on the board
CAN1_RXD: J3.4; also elsewhere on the board
CAN1_TXD: J2.4; also elsewhere on the board
ECU_GND: J2.1; also elsewhere on the board
Q1C: J3.3; also elsewhere on the board
Q2C: J3.2; also elsewhere on the board
Q3C: J3.1; also elsewhere on the board
Q4C: J2.3; also elsewhere on the board

Notes on the sheet:
GND
G25
G21
G33
G23
G19
G22
3V3

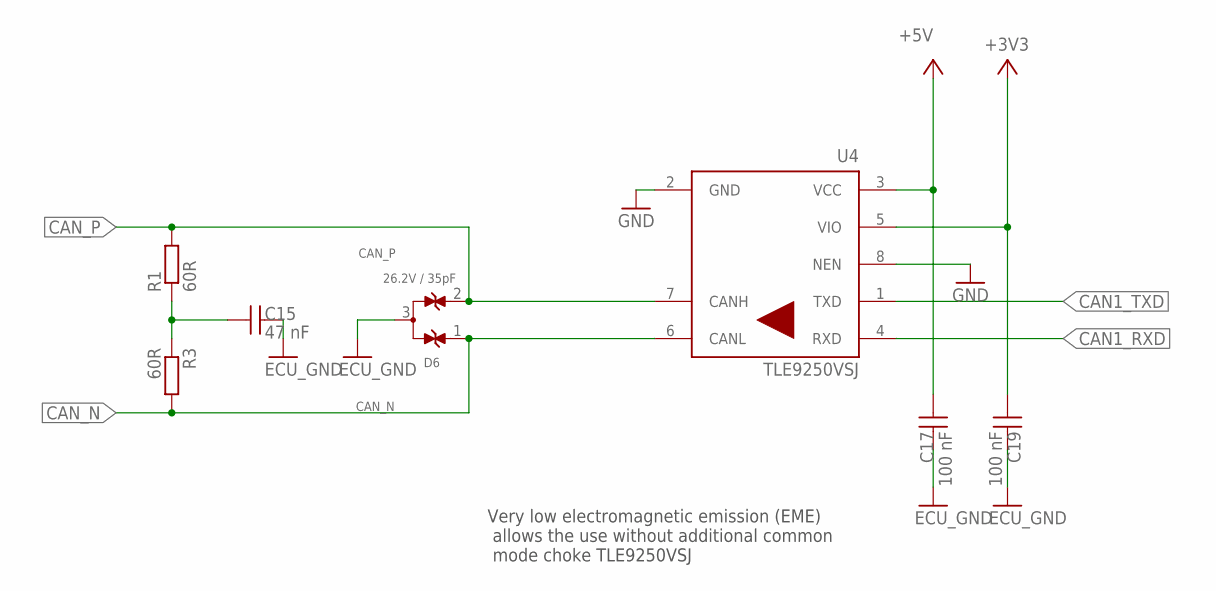
[picture p96: schematic Hutschienenmoped_24V.sch, sheet 5]

Parts:
C15: 47 nF; WCAP-CSGP_0805_H0.8_R
C17, C19: 100 nF; WCAP-CSGP_0805_H0.8_R
D6: 26.2V / 35pF; WE-TVS_SOT23-3L
R1, R3: 60R; R0805
U4: TLE9250VSJ; SOIC127P602X173-8N-V

Connections:
+3V3: C19.1, U4.5 (VIO); also elsewhere on the board
+5V: C17.1, U4.3 (VCC); also elsewhere on the board
CAN1_RXD: U4.4 (RXD); also elsewhere on the board
CAN1_TXD: U4.1 (TXD); also elsewhere on the board
CAN_N: D6.1, R3.2, U4.6 (CANL); also elsewhere on the board
CAN_P: D6.2, R1.2, U4.7 (CANH); also elsewhere on the board
ECU_GND: C15.2, C17.2, C19.2, D6.3, U4.2 (GND), U4.8 (NEN); also elsewhere on the board
unnamed: C15.1, R1.1, R3.1

Notes on the sheet:
Very low electromagnetic emission (EME) allows the use without additional common mode choke TLE9250VSJ

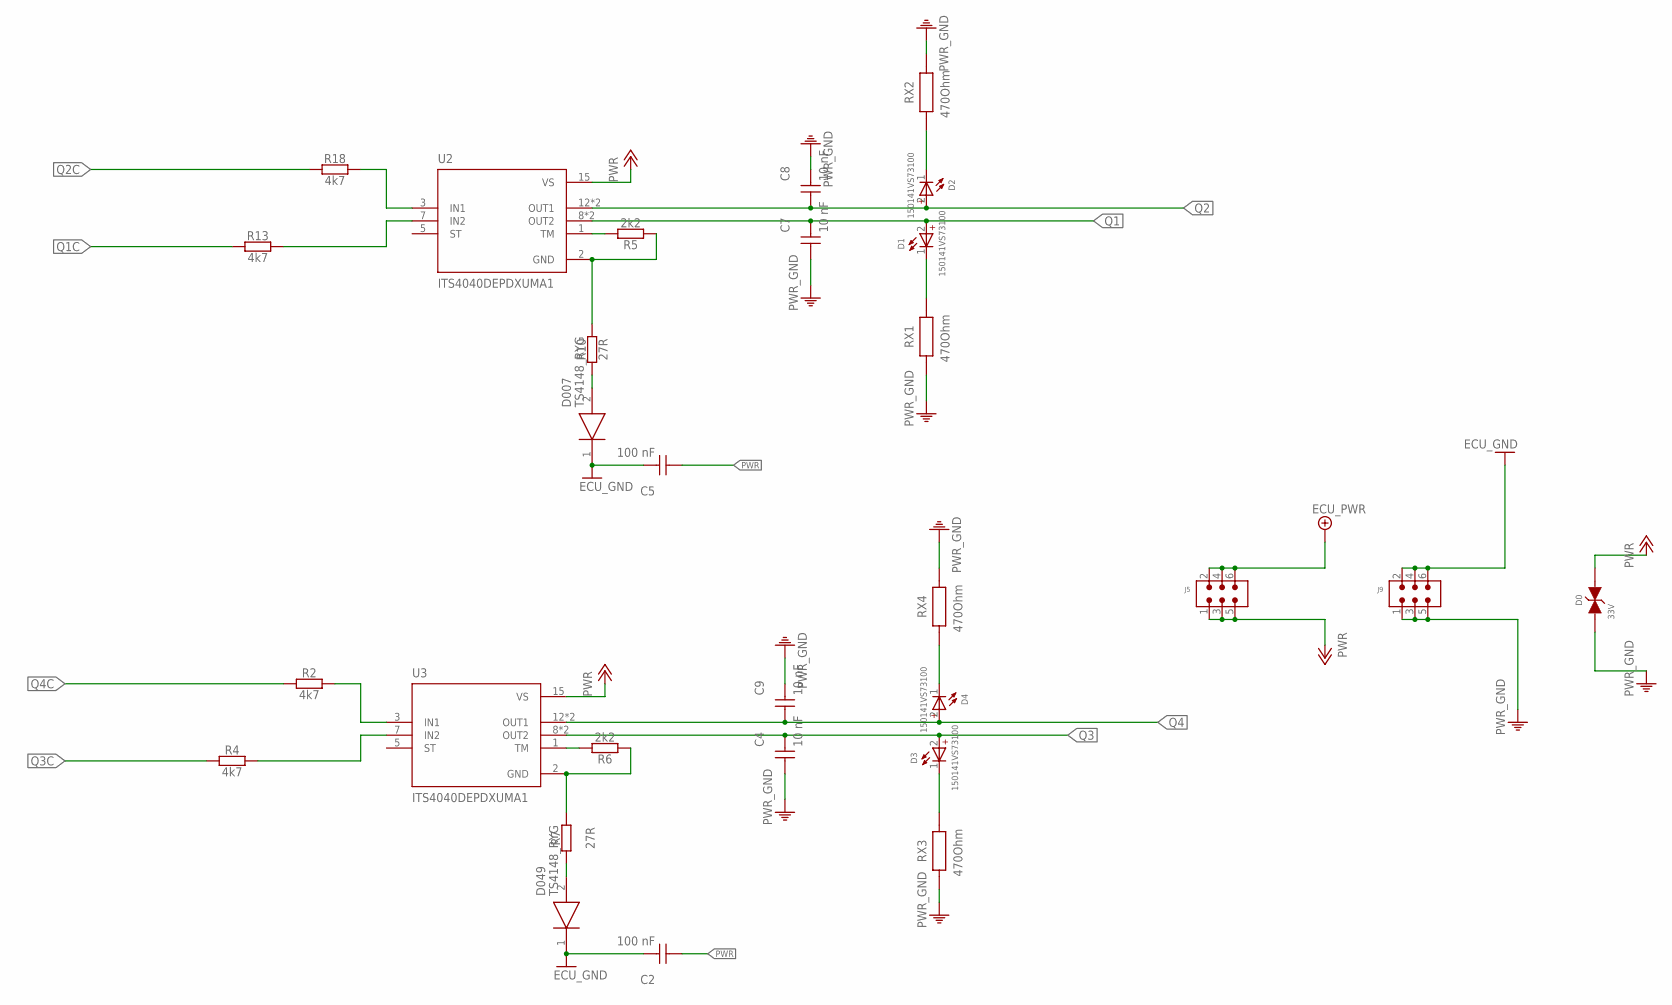
[picture p97: schematic Hutschienenmoped_24V.sch, sheet 6]

Parts:
C2, C5: 100 nF; WCAP-CSGP_0805_H0.8_R
C4, C7, C8, C9: 10 nF; WCAP-CSGP_0805_H0.8_R
D0: 33V; WE-TVSP_DO-214AB_BIDIRECTIONAL
D1, D2, D3, D4: 150141VS73100; WL-SMTW_3528
D007, D049: TS4148_RYG; DIOC2012X95N
J5, J9: 6130XX21121_61300621121; 61300621121
R2, R4, R13, R18: 4k7; R0805
R5, R6: 2k2; R0805
R7, R10: 27R; R0805
RX1, RX2, RX3, RX4: 470Ohm; WRIS-KWKB_0612
U2, U3: ITS4040DEPDXUMA1; SOP65P600X115-15N

Connections:
ECU_GND: C2.2, C5.2, D007.1 (K), D049.1 (K), J9.2, J9.4, J9.6; also elsewhere on the board
ECU_PWR: J5.2, J5.4, J5.6; also elsewhere on the board
unnamed: D4.1 (-), RX4.1
unnamed: R2.2, U3.3 (IN1)
unnamed: R6.2, U3.1 (TM)
unnamed: R4.2, U3.7 (IN2)
unnamed: R5.2, U2.1 (TM)
unnamed: D2.1 (-), RX2.1
unnamed: D1.1 (-), RX1.2
unnamed: D3.1 (-), RX3.2
unnamed: R18.2, U2.3 (IN1)
unnamed: D049.2 (A), R7.1
unnamed: D007.2 (A), R10.1
unnamed: R6.1, R7.2, U3.2 (GND)
unnamed: R13.2, U2.7 (IN2)
unnamed: R5.1, R10.2, U2.2 (GND)
PWR: C2.1, C5.1, D0.2, J5.1, J5.3, J5.5, U2.15 (VS), U3.15 (VS); also elsewhere on the board
PWR_GND: C4.1, C7.1, C8.2, C9.2, D0.1, J9.1, J9.3, J9.5, RX1.1, RX2.2, RX3.1, RX4.2; also elsewhere on the board
Q1: C7.2, D1.2 (+), U2.8 (OUT2), U2.10 (OUT2); also elsewhere on the board
Q1C: R13.1; also elsewhere on the board
Q2: C8.1, D2.2 (+), U2.12 (OUT1), U2.14 (OUT1); also elsewhere on the board
Q2C: R18.1; also elsewhere on the board
Q3: C4.2, D3.2 (+), U3.8 (OUT2), U3.10 (OUT2); also elsewhere on the board
Q3C: R4.1; also elsewhere on the board
Q4: C9.1, D4.2 (+), U3.12 (OUT1), U3.14 (OUT1); also elsewhere on the board
Q4C: R2.1; also elsewhere on the board

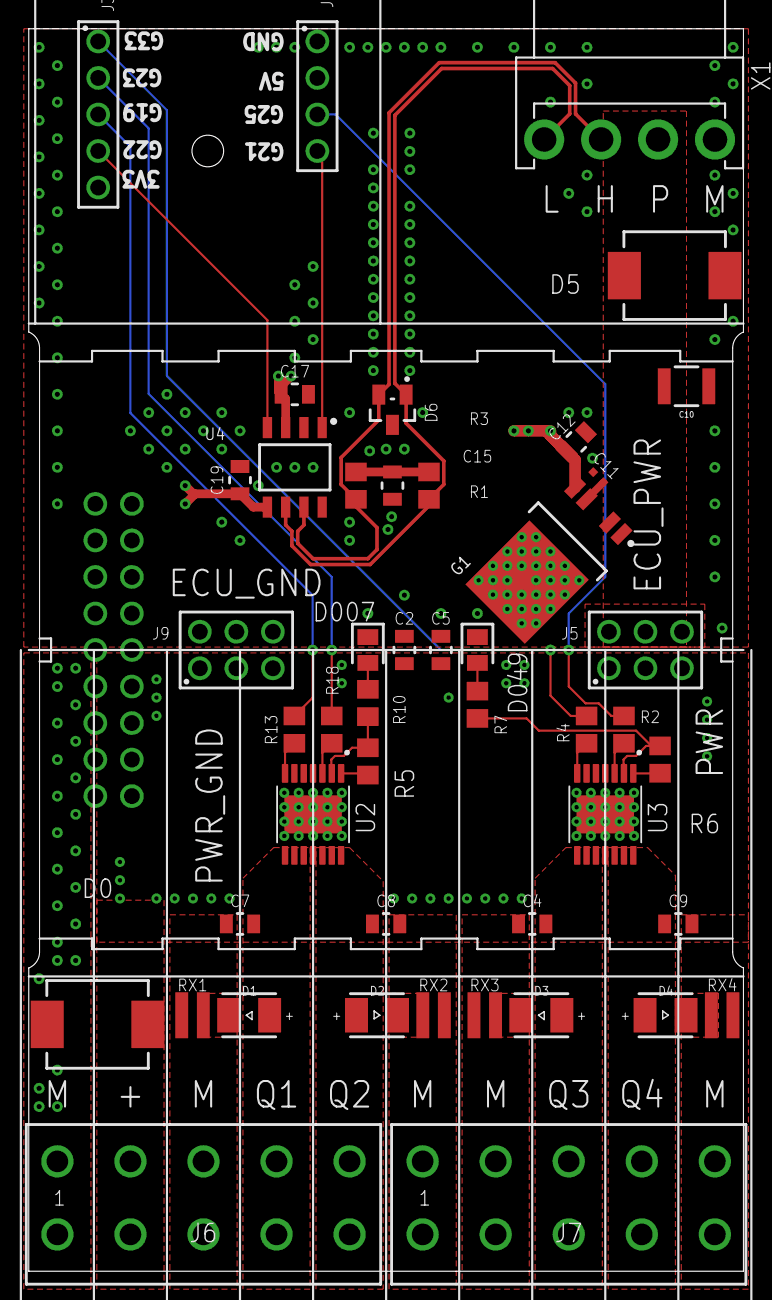
[picture p98: board Hutschienenmoped_24V.brd from above]

Board: 4 copper layers, 49.7 x 86.4 mm, 47 parts (1 on the bottom side), 34 nets.
