Meisterschulen-am-Ostbahnhof-Munchen/ISOBUS_Hardware/C3_Stamp/M5_STACK_STAMP_C3_ISOBUS_DTF.brd

## EAGLE design C3_Stamp/M5_STACK_STAMP_C3_ISOBUS_DTF.brd (2022-06-30)

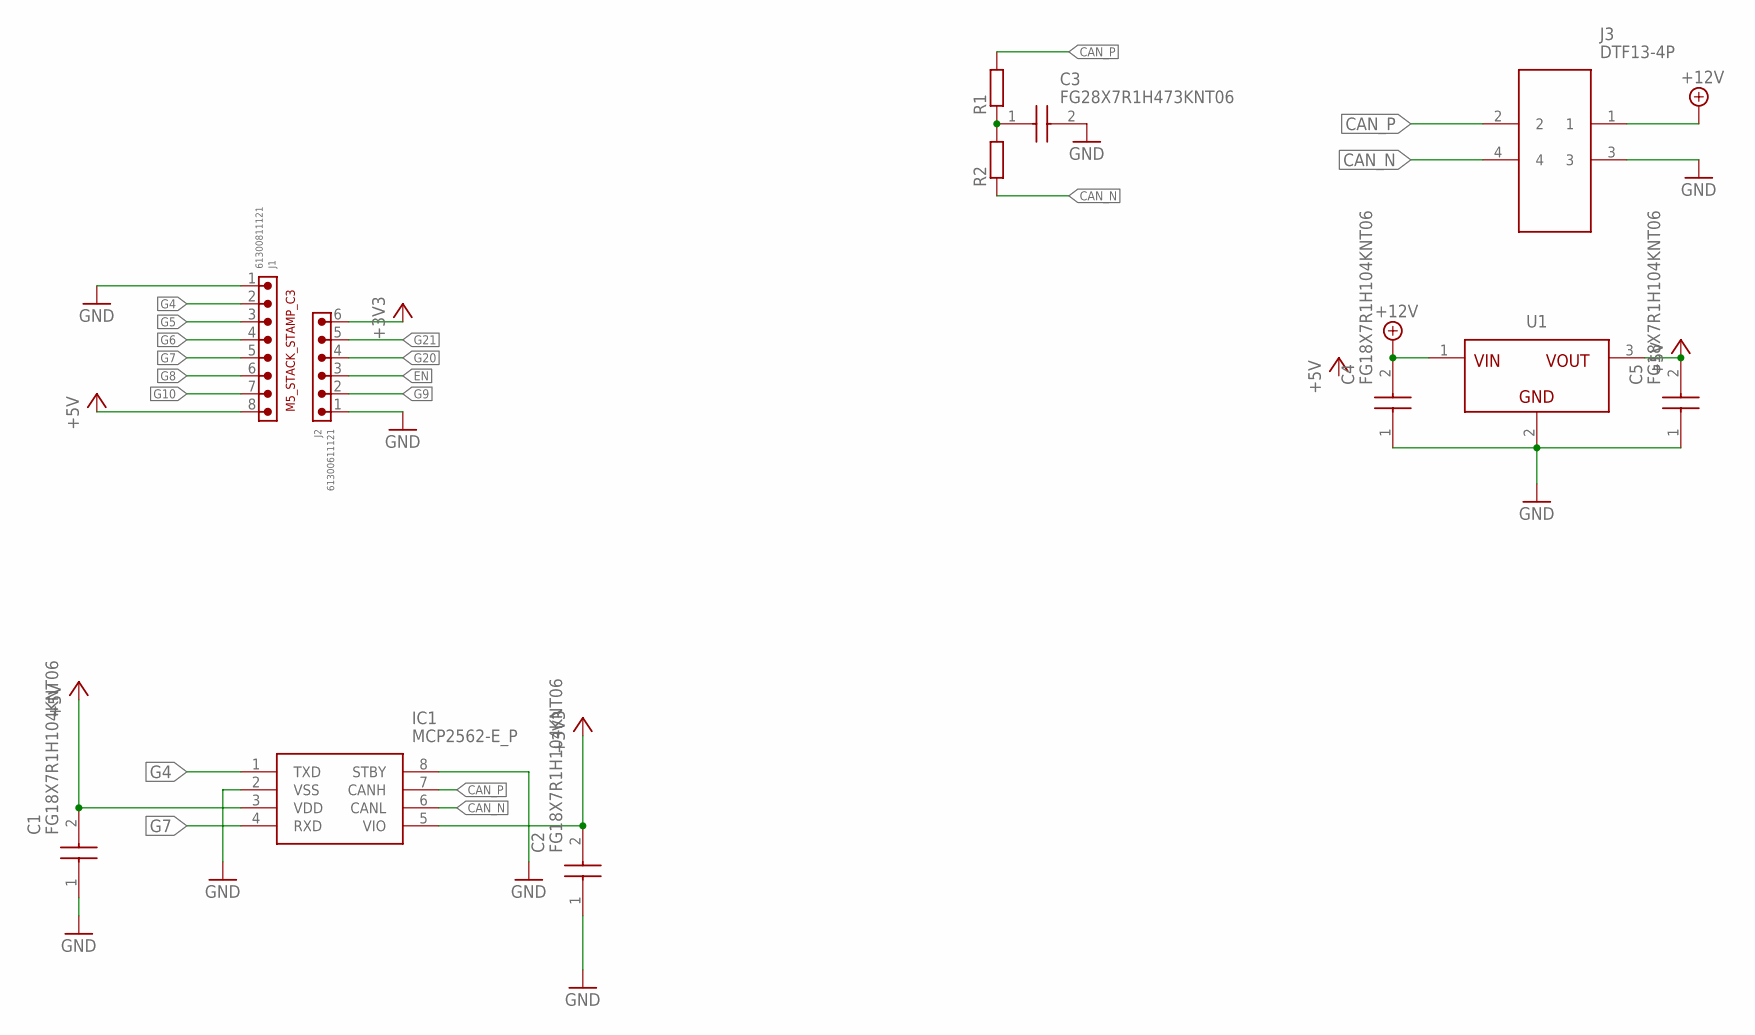
[picture p99: schematic M5_STACK_STAMP_C3_ISOBUS_DTF.sch]

Parts:
C1, C2, C4, C5: FG18X7R1H104KNT06; FG18C0G1H101JNT06
C3: FG28X7R1H473KNT06; FG28
IC1: MCP2562-E_P; DIP781W56P254L950H533Q8N
J1: 61300811121
J2: 61300611121
J3: DTF13-4P; DTF134P
R1, R2: R-EU_0204/7; 0204/7
U1: MAGI³C-FDSM_SIP-3_173010542_173XXXX42; MAGI³C-FDSM_173XXXX42
U$1: M5_STACK_STAMP_C3

Connections:
+3V3: C2.2, IC1.5 (VIO), J2.6
+5V: C1.2, C5.2, IC1.3 (VDD), J1.8, U1.3 (VOUT)
+12V: C4.2, J3.1, U1.1 (VIN)
CAN_N: IC1.6 (CANL), J3.4, R2.1
CAN_P: IC1.7 (CANH), J3.2, R1.2
EN: J2.3
G4: IC1.1 (TXD), J1.2
G5: J1.3
G6: J1.4
G7: IC1.4 (RXD), J1.5
G8: J1.6
G9: J2.2
G10: J1.7
G20: J2.4
G21: J2.5
GND: C1.1, C2.1, C3.2, C4.1, C5.1, IC1.2 (VSS), IC1.8 (STBY), J1.1, J2.1, J3.3, U1.2 (GND)
unnamed: C3.1, R1.1, R2.2

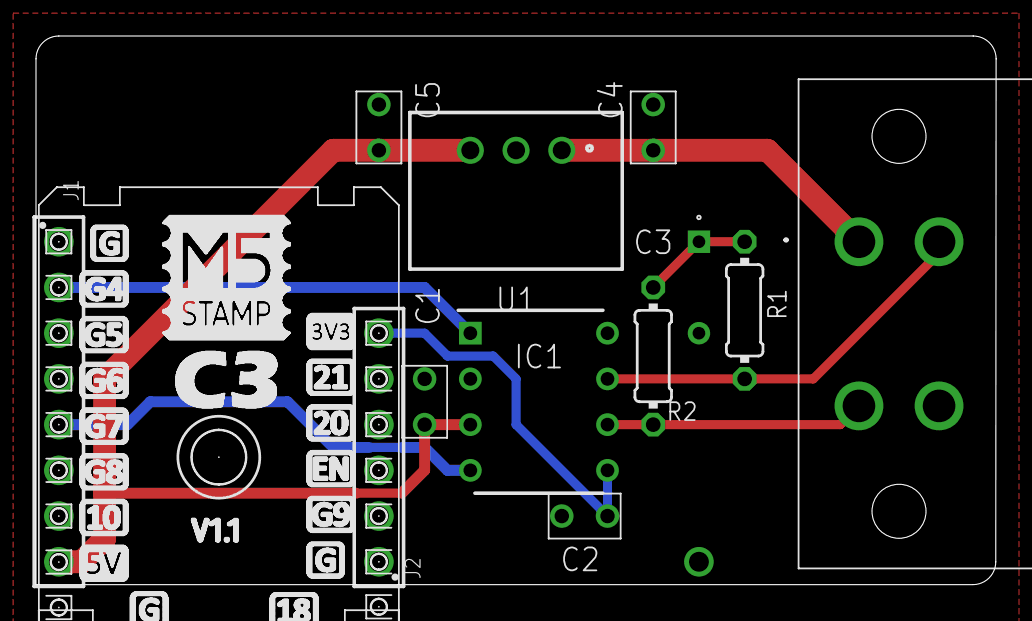
[picture p100: board M5_STACK_STAMP_C3_ISOBUS_DTF.brd from above]

Board: 2 copper layers, 53.3 x 30.5 mm, 13 parts (0 on the bottom side), 9 nets.
