Meisterschulen-am-Ostbahnhof-Munchen/ISOBUS_Hardware/S3/ISOBUS_Hardware_S3.brd

## EAGLE design S3/ISOBUS_Hardware_S3.brd (2022-06-30)

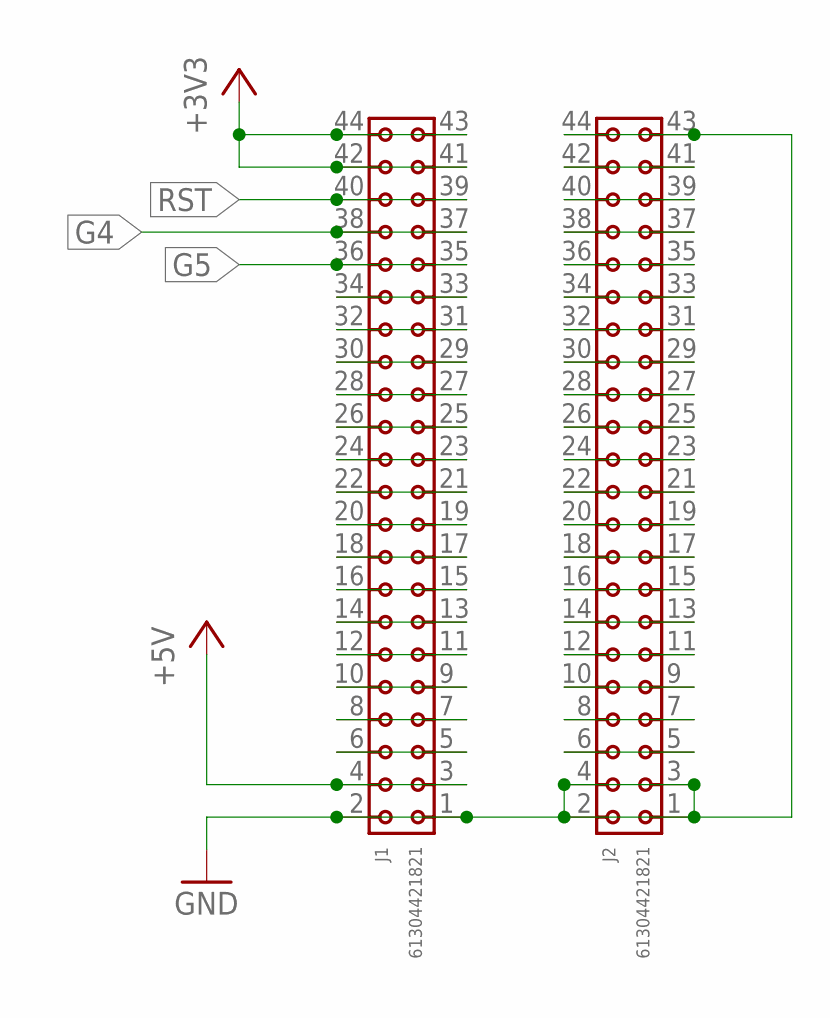
[picture p101: schematic ISOBUS_Hardware_S3.sch, sheet 1]

Parts:
J1, J2: 61304421821

Connections:
+3V3: J1.41, J1.42, J1.43, J1.44; also elsewhere on the board
+5V: J1.3, J1.4; also elsewhere on the board
G4: J1.37, J1.38; also elsewhere on the board
G5: J1.35, J1.36; also elsewhere on the board
GND: J1.1, J1.2, J2.1, J2.2, J2.3, J2.4, J2.43, J2.44; also elsewhere on the board
unnamed: J1.33, J1.34
unnamed: J1.31, J1.32
unnamed: J1.29, J1.30
unnamed: J1.27, J1.28
unnamed: J1.25, J1.26
unnamed: J1.23, J1.24
unnamed: J1.21, J1.22
unnamed: J1.19, J1.20
unnamed: J1.17, J1.18
unnamed: J1.15, J1.16
unnamed: J1.13, J1.14
unnamed: J1.11, J1.12
unnamed: J1.9, J1.10
unnamed: J1.7, J1.8
unnamed: J1.5, J1.6
unnamed: J2.5, J2.6
unnamed: J2.7, J2.8
unnamed: J2.9, J2.10
unnamed: J2.11, J2.12
unnamed: J2.13, J2.14
unnamed: J2.15, J2.16
unnamed: J2.17, J2.18
unnamed: J2.19, J2.20
unnamed: J2.21, J2.22
unnamed: J2.23, J2.24
unnamed: J2.25, J2.26
unnamed: J2.27, J2.28
unnamed: J2.29, J2.30
unnamed: J2.31, J2.32
unnamed: J2.33, J2.34
unnamed: J2.35, J2.36
unnamed: J2.37, J2.38
unnamed: J2.39, J2.40
unnamed: J2.41, J2.42
RST: J1.39, J1.40

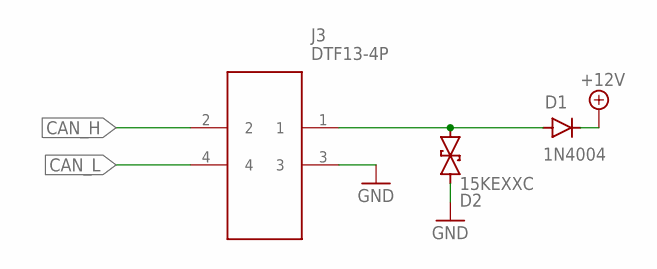
[picture p102: schematic ISOBUS_Hardware_S3.sch, sheet 2]

Parts:
D1: 1N4004; DO-41
D2: 15KEXXC; CB429-17
J3: DTF13-4P; DTF134P

Connections:
+12V: D1.C; also elsewhere on the board
CAN_H: J3.2; also elsewhere on the board
CAN_L: J3.4; also elsewhere on the board
GND: D2.A (1), J3.3; also elsewhere on the board
unnamed: D1.A, D2.C (2), J3.1

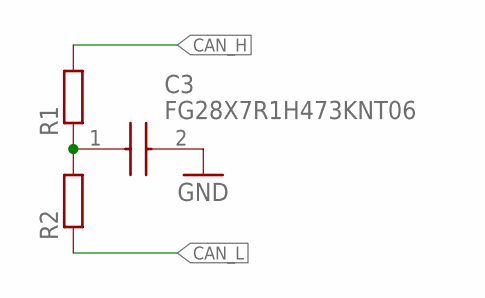
[picture p103: schematic ISOBUS_Hardware_S3.sch, sheet 3]

Parts:
C3: FG28X7R1H473KNT06; FG28
R1, R2: R-EU_0204/7; 0204/7

Connections:
CAN_H: R1.2; also elsewhere on the board
CAN_L: R2.1; also elsewhere on the board
GND: C3.2; also elsewhere on the board
unnamed: C3.1, R1.1, R2.2

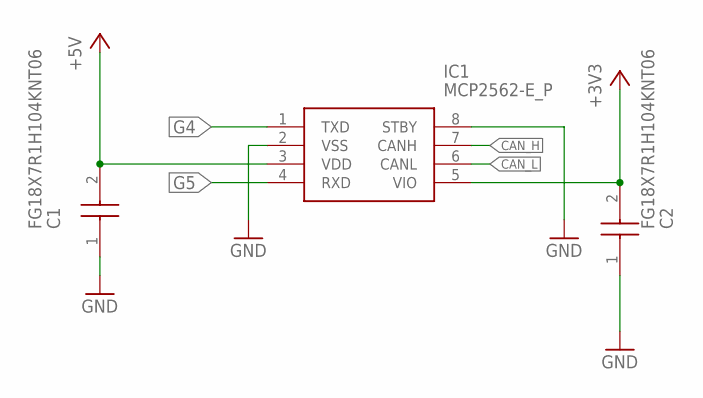
[picture p104: schematic ISOBUS_Hardware_S3.sch, sheet 4]

Parts:
C1, C2: FG18X7R1H104KNT06; FG18C0G1H101JNT06
IC1: MCP2562-E_P; DIP781W56P254L950H533Q8N

Connections:
+3V3: C2.2, IC1.5 (VIO); also elsewhere on the board
+5V: C1.2, IC1.3 (VDD); also elsewhere on the board
CAN_H: IC1.7 (CANH); also elsewhere on the board
CAN_L: IC1.6 (CANL); also elsewhere on the board
G4: IC1.1 (TXD); also elsewhere on the board
G5: IC1.4 (RXD); also elsewhere on the board
GND: C1.1, C2.1, IC1.2 (VSS), IC1.8 (STBY); also elsewhere on the board

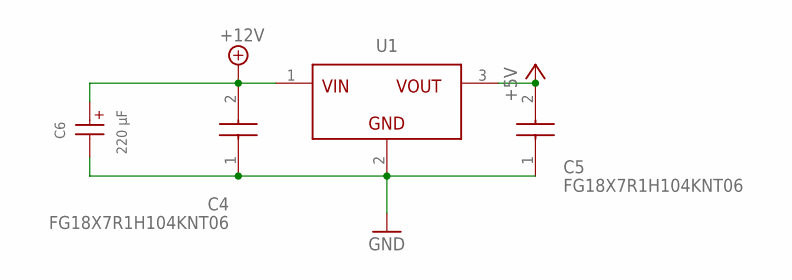
[picture p105: schematic ISOBUS_Hardware_S3.sch, sheet 5]

Parts:
C4, C5: FG18X7R1H104KNT06; FG18C0G1H101JNT06
C6: 220 µF; WCAP-ATG8_6.3X11(DXL)
U1: MAGI³C-FDSM_SIP-3_173010542_173XXXX42; MAGI³C-FDSM_173XXXX42

Connections:
+5V: C5.2, U1.3 (VOUT); also elsewhere on the board
+12V: C4.2, C6.1 (+), U1.1 (VIN); also elsewhere on the board
GND: C4.1, C5.1, C6.2 (-), U1.2 (GND); also elsewhere on the board

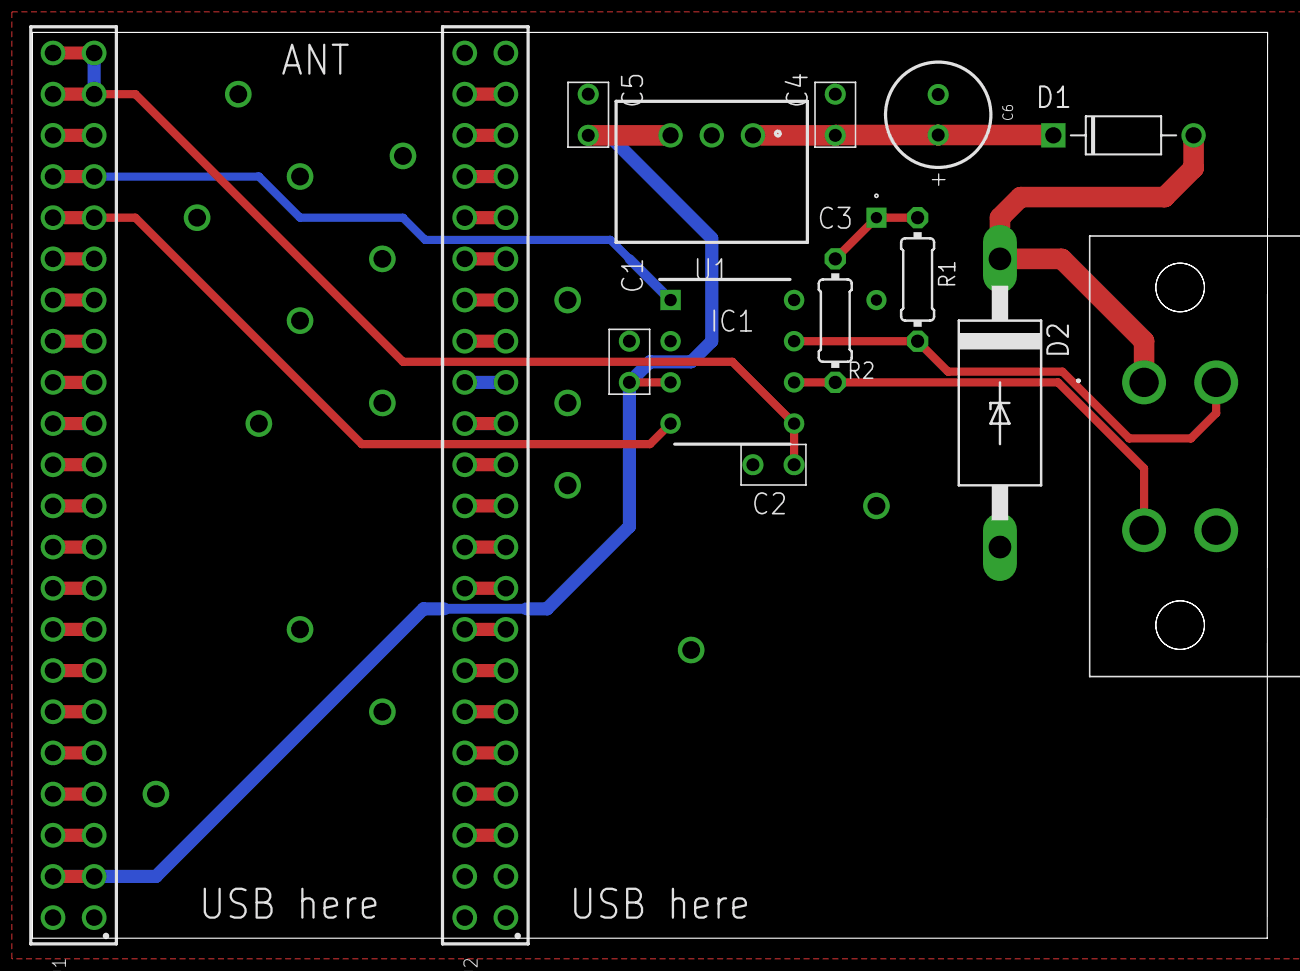
[picture p106: board ISOBUS_Hardware_S3.brd from above]

Board: 2 copper layers, 76.2 x 55.9 mm, 15 parts (0 on the bottom side), 45 nets.
