Meisterschulen-am-Ostbahnhof-Munchen/ISOBUS_Hardware/C3_Stamp/M5_STACK_STAMP_C3_ISOBUS_JSTex.brd

## EAGLE design C3_Stamp/M5_STACK_STAMP_C3_ISOBUS_JSTex.brd (2022-06-30)

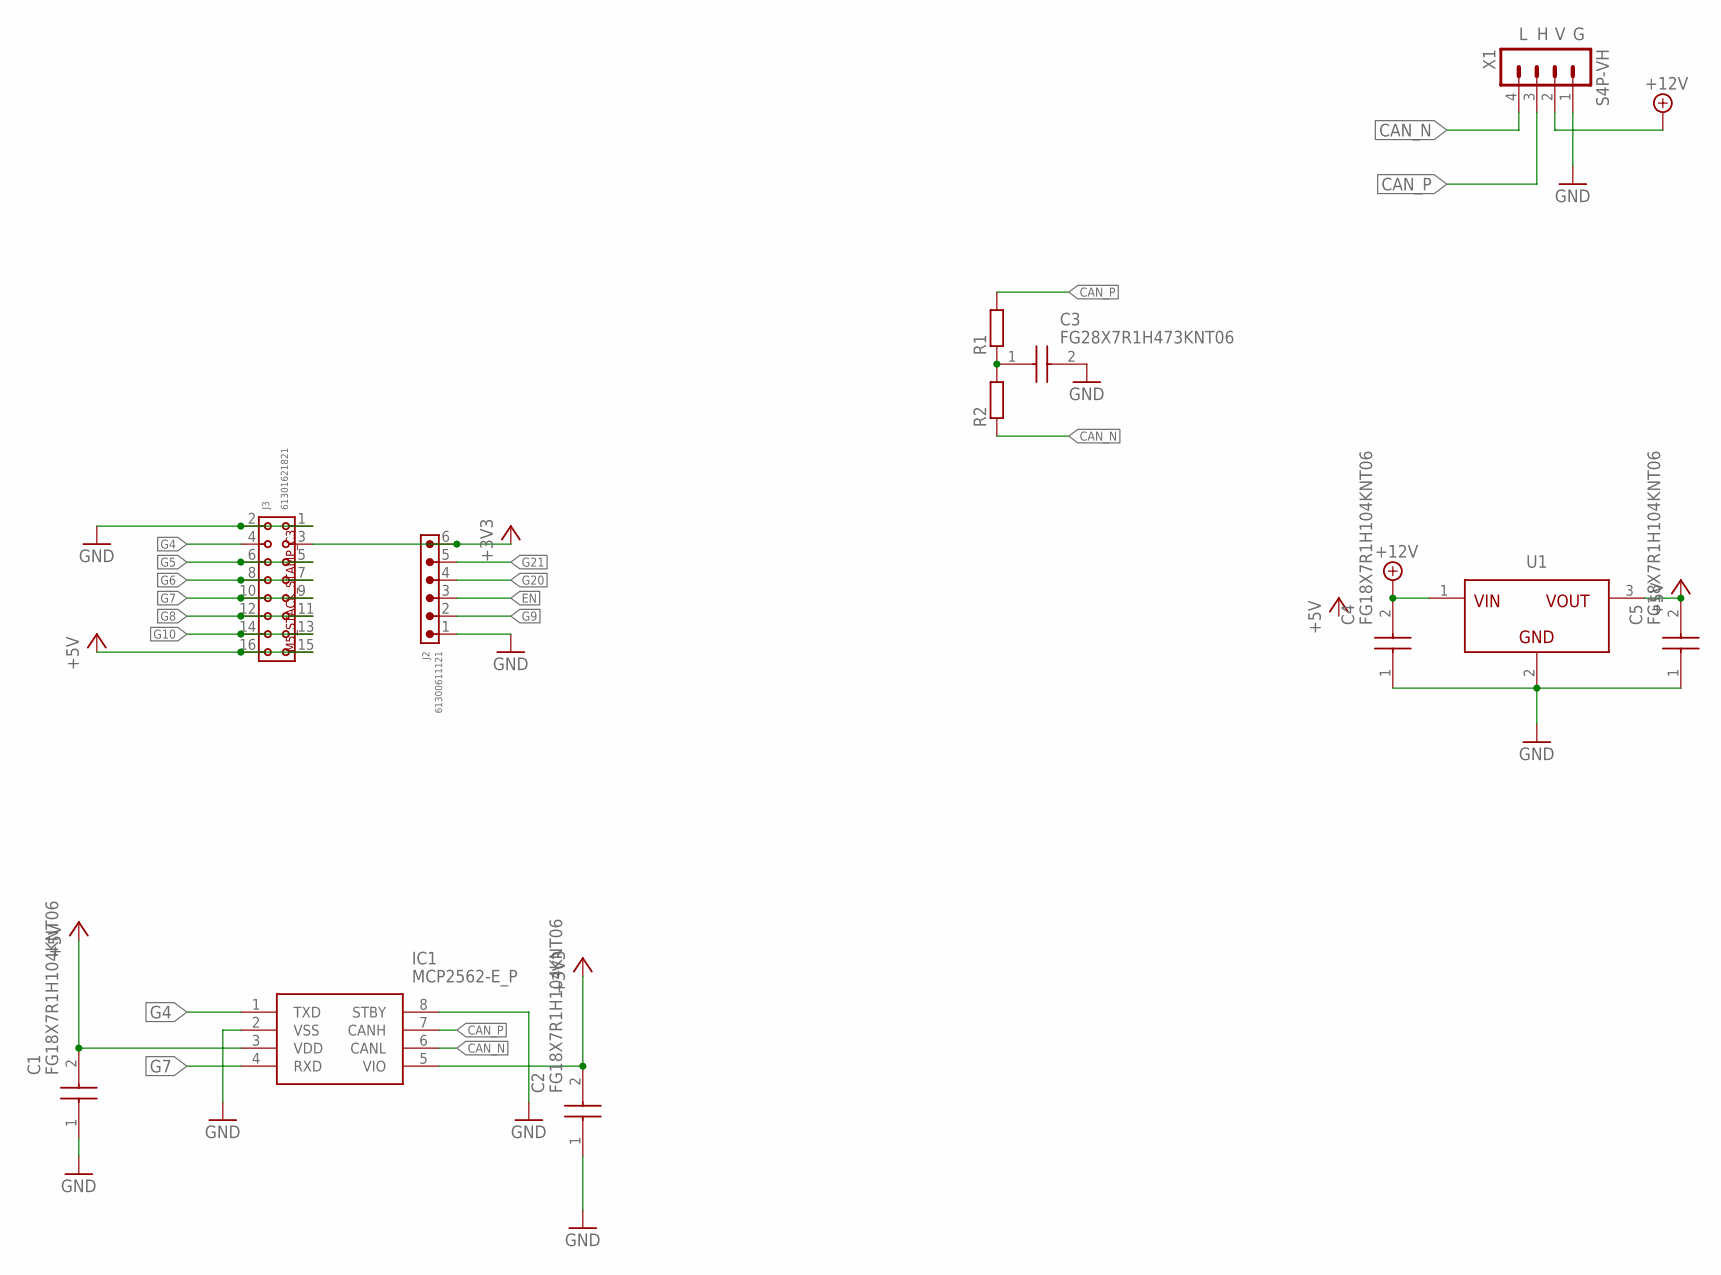
[picture p107: schematic M5_STACK_STAMP_C3_ISOBUS_JSTex.sch]

Parts:
C1, C2, C4, C5: FG18X7R1H104KNT06; FG18C0G1H101JNT06
C3: FG28X7R1H473KNT06; FG28
IC1: MCP2562-E_P; DIP781W56P254L950H533Q8N
J2: 61300611121
J3: 61301621821
R1, R2: R-EU_0204/7; 0204/7
U1: MAGI³C-FDSM_SIP-3_173010542_173XXXX42; MAGI³C-FDSM_173XXXX42
U$1: M5_STACK_STAMP_C3
X1: S4P-VH

Connections:
+3V3: C2.2, IC1.5 (VIO), J2.6, J3.3
+5V: C1.2, C5.2, IC1.3 (VDD), J3.15, J3.16, U1.3 (VOUT)
+12V: C4.2, U1.1 (VIN), X1.2
CAN_N: IC1.6 (CANL), R2.1, X1.4
CAN_P: IC1.7 (CANH), R1.2, X1.3
EN: J2.3
G4: IC1.1 (TXD), J3.4
G5: J3.5, J3.6
G6: J3.7, J3.8
G7: IC1.4 (RXD), J3.9, J3.10
G8: J3.11, J3.12
G9: J2.2
G10: J3.13, J3.14
G20: J2.4
G21: J2.5
GND: C1.1, C2.1, C3.2, C4.1, C5.1, IC1.2 (VSS), IC1.8 (STBY), J2.1, J3.1, J3.2, U1.2 (GND), X1.1
unnamed: C3.1, R1.1, R2.2

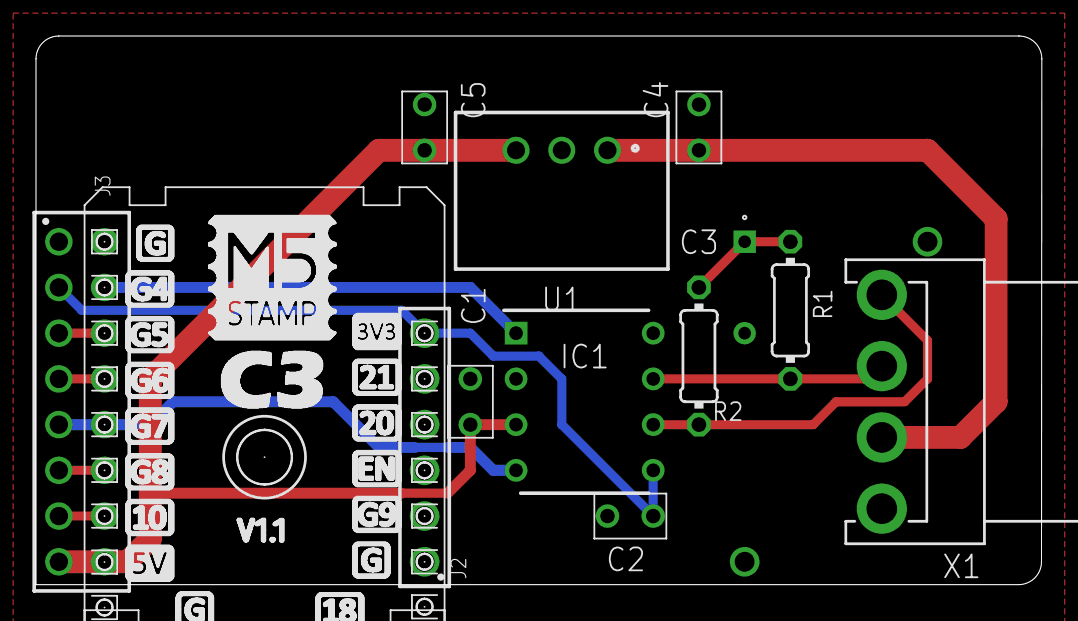
[picture p108: board M5_STACK_STAMP_C3_ISOBUS_JSTex.brd from above]

Board: 2 copper layers, 55.9 x 30.5 mm, 13 parts (0 on the bottom side), 13 nets.
