Meisterschulen-am-Ostbahnhof-Munchen/ISOBUS_Hardware/Atomic_V1.0/Atomic_Stick.brd

## EAGLE design Atomic_V1.0/Atomic_Stick.brd (2021-08-06)

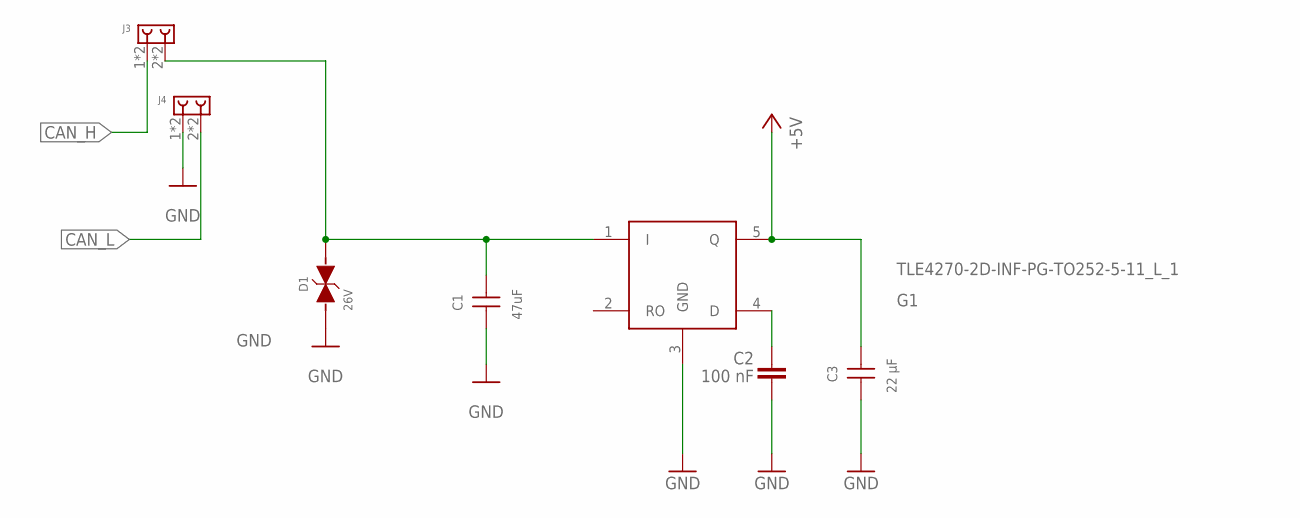
[picture p109: schematic Atomic_Stick.sch, sheet 1]

Parts:
C1: 47uF; WCAP-CSGP_1210_H2.5
C2: 100 nF; WCAP-CSGP_0402
C3: 22 µF; WCAP-CSGP_0805_H1.25_R
D1: 26V; WE-TVSP_DO-214AC_BIDIRECTIONAL
G1: TLE4270-2D-INF-PG-TO252-5-11_L_1; INF-PG-TO252-5-11_L_1PRIMARY
J3, J4: 695402400222

Connections:
+5V: C3.2, G1.5 (Q); also elsewhere on the board
+12V: C1.2, D1.2, G1.1 (I), J3.2, J3.A2 (2)
CAN_H: J3.1, J3.A1 (1); also elsewhere on the board
CAN_L: J4.2, J4.A2 (2); also elsewhere on the board
GND: C1.1, C2.2, C3.1, D1.1, G1.3 (GND), J4.1, J4.A1 (1); also elsewhere on the board
unnamed: C2.1, G1.4 (D)
