Meisterschulen-am-Ostbahnhof-Munchen/ISOBUS_Hardware/Atomic_V1.0/Atomic_V1.0.brd

## EAGLE design Atomic_V1.0/Atomic_V1.0.brd (2021-07-08)

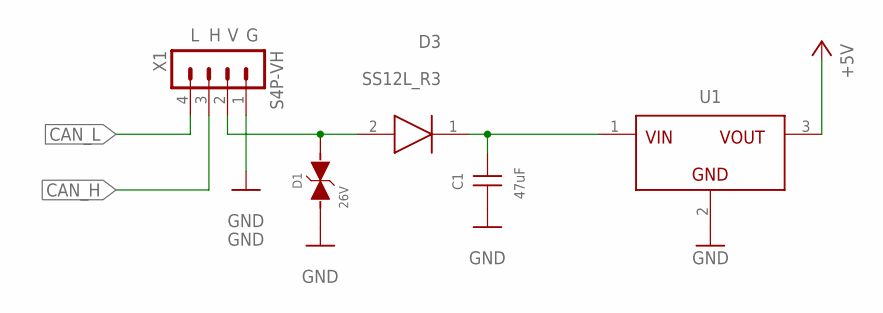
[picture p113: schematic Atomic_V1.0.sch, sheet 1]

Parts:
C1: 47uF; WCAP-CSGP_1210_H2.5
D1: 26V; WE-TVSP_DO-214AC_BIDIRECTIONAL
D3: SS12L_R3; SODFL3618X143N
U1: MAGI³C-FDSM_SIP-3_173010542_173XXXX42; MAGI³C-FDSM_173XXXX42
X1: S4P-VH

Connections:
+5V: U1.3 (VOUT); also elsewhere on the board
+12V: D1.2, D3.2 (A), X1.2
CAN_H: X1.3; also elsewhere on the board
CAN_L: X1.4; also elsewhere on the board
GND: C1.1, D1.1, U1.2 (GND), X1.1; also elsewhere on the board
unnamed: C1.2, D3.1 (K), U1.1 (VIN)


Parts:
J1: 6130XX11121_61300411121; 61300411121
J2: 6130XX11121_61300511121; 61300511121

Connections:
+3V3: J2.5; also elsewhere on the board
+5V: J1.2; also elsewhere on the board
CAN1_RXD: J2.4; also elsewhere on the board
CAN1_TXD: J1.4; also elsewhere on the board
GND: J1.1; also elsewhere on the board

Notes on the sheet:
GND
G25
G21
G33
G23
G19
G22
3V3


Parts:
C15: 47 nF; WCAP-CSGP_0402
C17, C19: 100 nF; WCAP-CSGP_0402
D6: 26.2V / 35pF; WE-TVS_SOT23-3L
R21, R22: 60.4R 1%; WCAP-CSRF_0402
U4: TLE9250VSJ; SOIC127P602X173-8N-V

Connections:
+3V3: C19.1, U4.5 (VIO); also elsewhere on the board
+5V: C17.1, U4.3 (VCC); also elsewhere on the board
CAN1_RXD: U4.4 (RXD); also elsewhere on the board
CAN1_TXD: U4.1 (TXD); also elsewhere on the board
CAN_H: D6.2, R22.2, U4.7 (CANH); also elsewhere on the board
CAN_L: D6.1, R21.1, U4.6 (CANL); also elsewhere on the board
GND: C15.2, C17.2, C19.2, D6.3, U4.2 (GND), U4.8 (NEN); also elsewhere on the board
unnamed: C15.1, R21.2, R22.1

Notes on the sheet:
Very low electromagnetic emission (EME) allows the use without additional common mode choke TLE9250VSJ

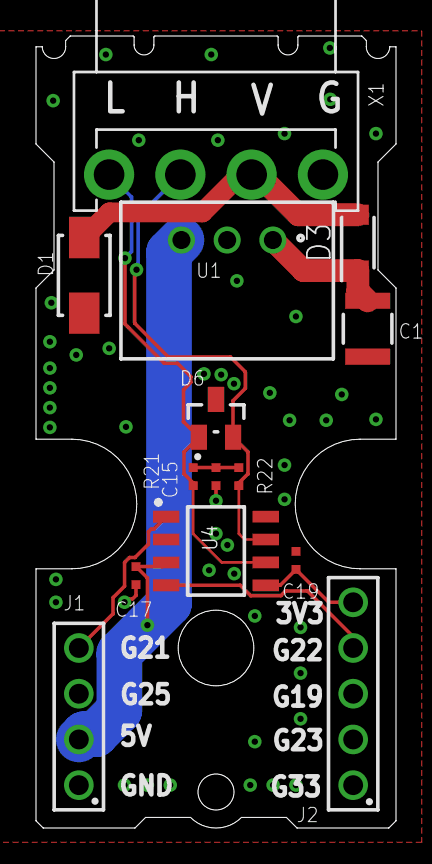
[picture p114: board Atomic_V1.0.brd from above]

Board: 2 copper layers, 20.0 x 44.0 mm, 14 parts (0 on the bottom side), 10 nets.
